Offlinedevice/Offlinedevice/3D/Pi5/Dock/readme

# Guide for Docking station for Offline device, Pi 5:

# Items needed for the build:
# * Small screwdriver and 6 pcs of M2 x 16 mm screws.
# * The 5 printed parts from the 3D files (optional also the dummy lid).
# * An official Raspberry PI 5 USB-power cable.
# * A HDMI- cable with micro-HDMI connector. Manufacturer: Zhonghua, Brand: TWOZOH, Model: ‎HD-012-1.0M
