Offlinedevice/Offlinedevice/3D/Pi5/Case/readme

# Case for:
# - Raspberry Pi 5
# - RTC battery
# - PN532 RFID module V3 
# - 5V 3007 Fan PWM Speed Adjustable CPU Cooling fan
# - Pi camera module 1, 2 or 3
