Offlinedevice/Offlinedevice/Bitcoin_wallet.png

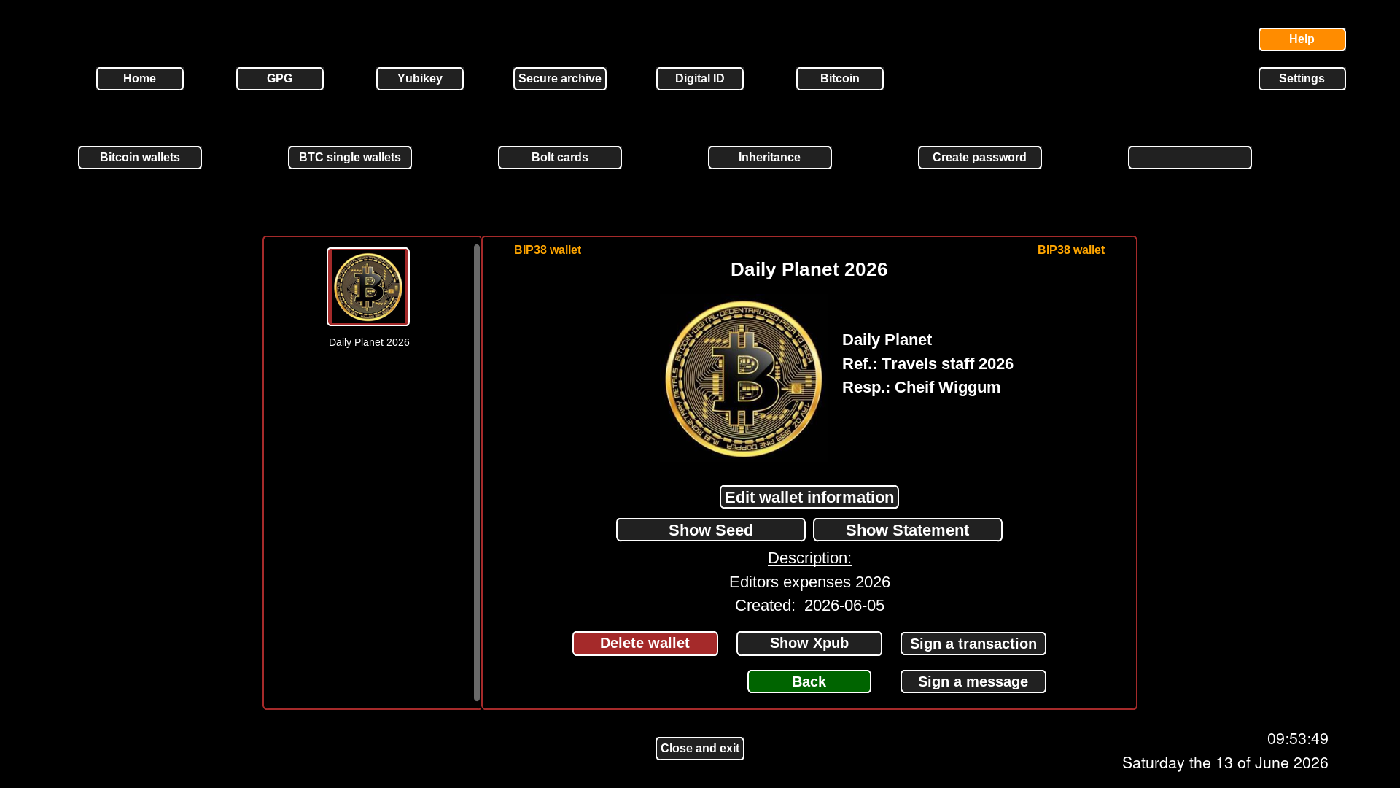
Bitcoin_wallet.png
