Offlinedevice/Offlinedevice/content/1_Welcome_Ethan_Soren.png

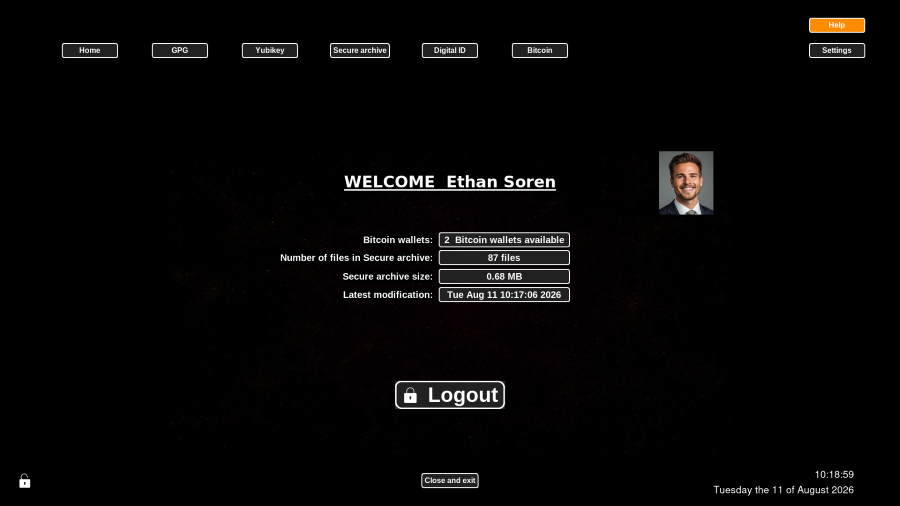
content/1_Welcome_Ethan_Soren.png
