Offlinedevice/Offlinedevice/content/3_1_Multisig_Signing_keys.PNG

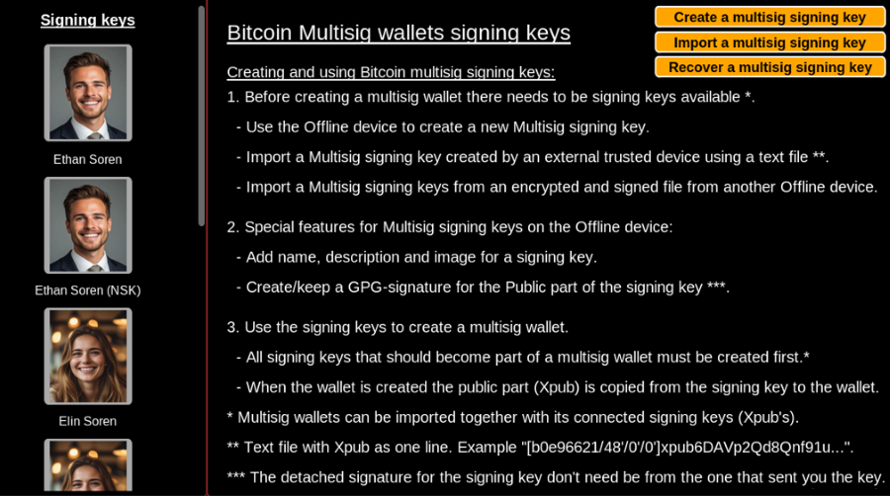
content/3_1_Multisig_Signing_keys.PNG
