Offlinedevice/Offlinedevice/images/black.jpg

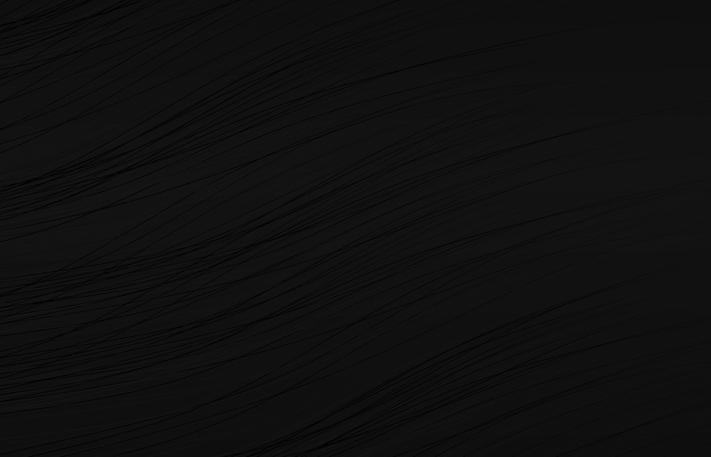
images/black.jpg
