Offlinedevice/Offlinedevice/images/blackbackground.jpg

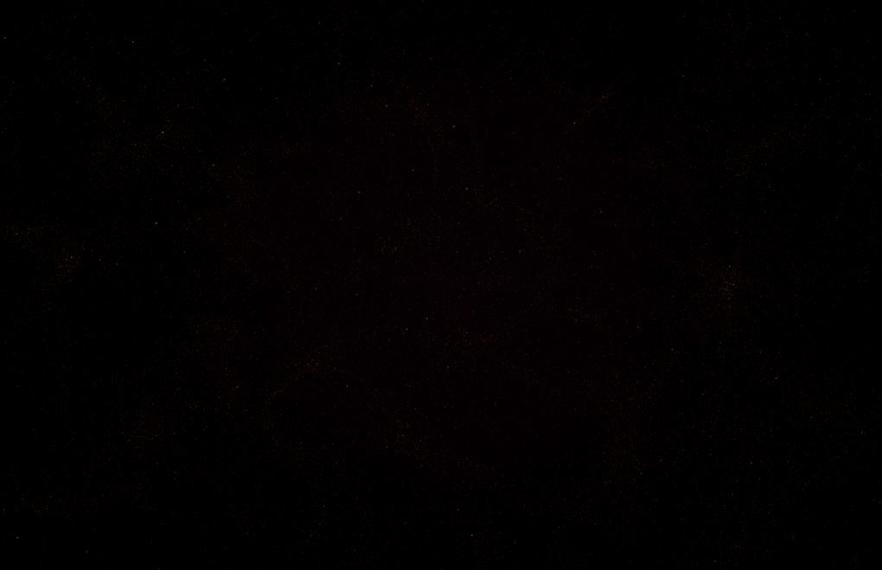
images/blackbackground.jpg
