Offlinedevice/Offlinedevice/images/bluebackground.jpg

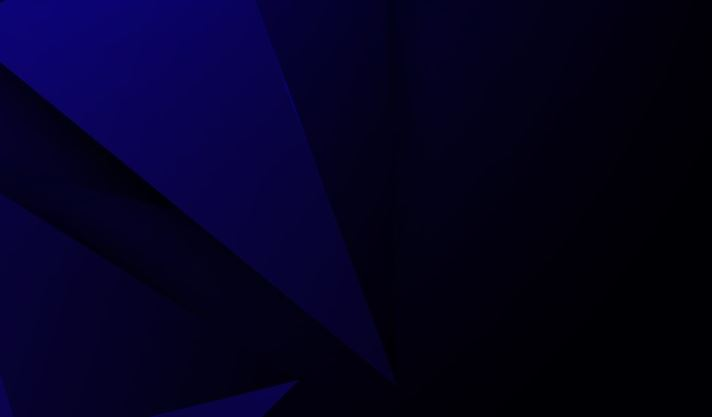
images/bluebackground.jpg
