Offlinedevice/Offlinedevice/images/bluewaves.jpg

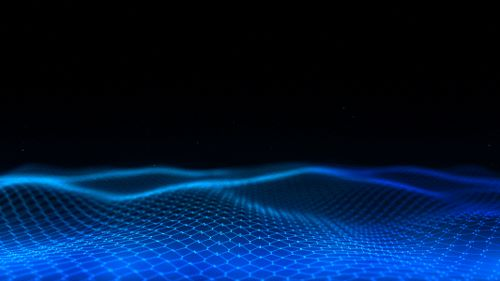
images/bluewaves.jpg
