Offlinedevice/Offlinedevice/images/boltcardbackground.JPG

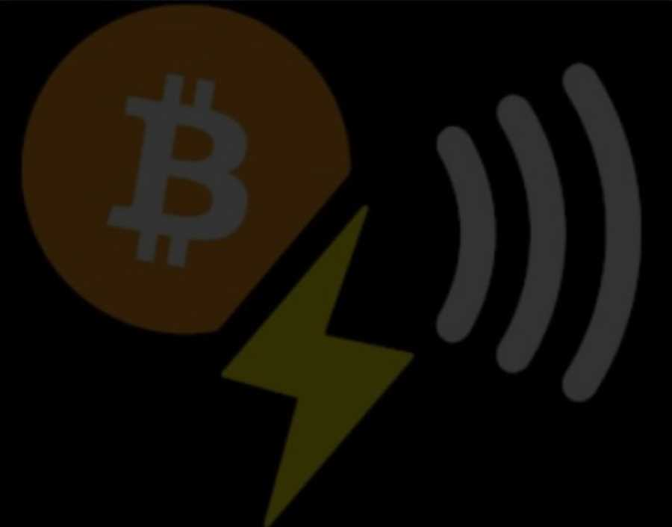
images/boltcardbackground.JPG
