Offlinedevice/Offlinedevice/images/darkbackground.jpg

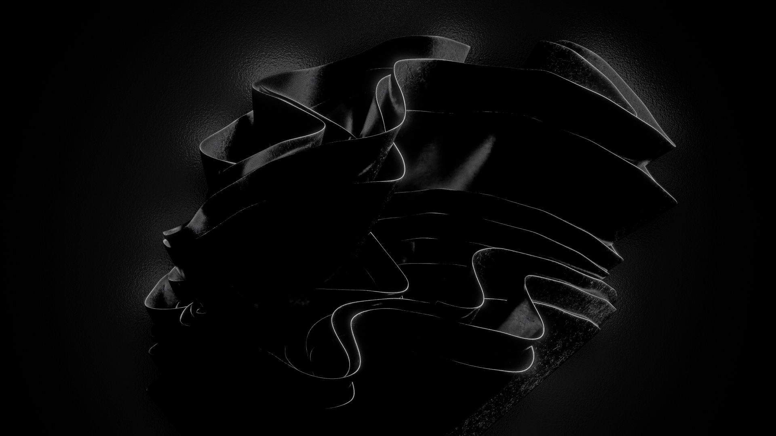
images/darkbackground.jpg
