Offlinedevice/Offlinedevice/images/darkbackgroundmid.jpg

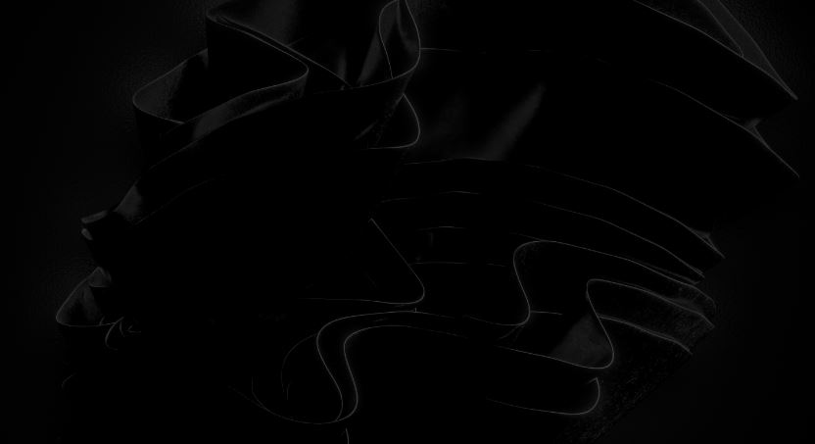
images/darkbackgroundmid.jpg
