Offlinedevice/Offlinedevice/images/GnuPGbackground.JPG

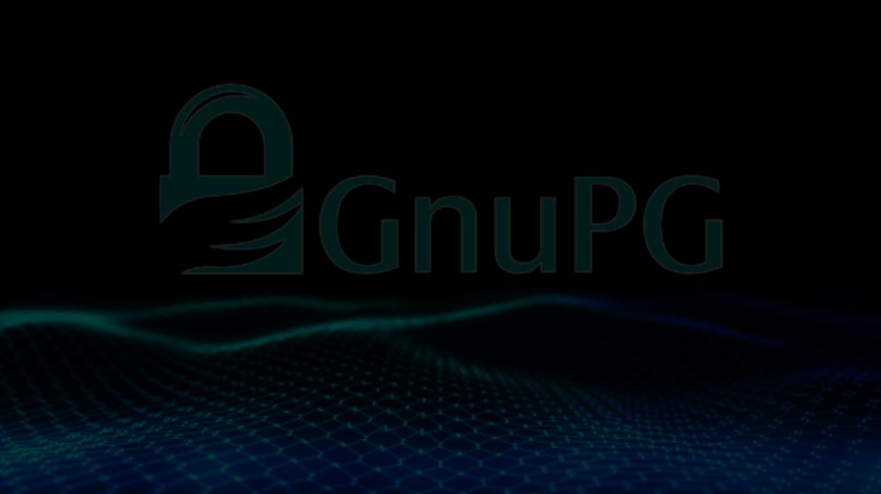
images/GnuPGbackground.JPG
