Offlinedevice/Offlinedevice/images/Inheritance_background.JPG

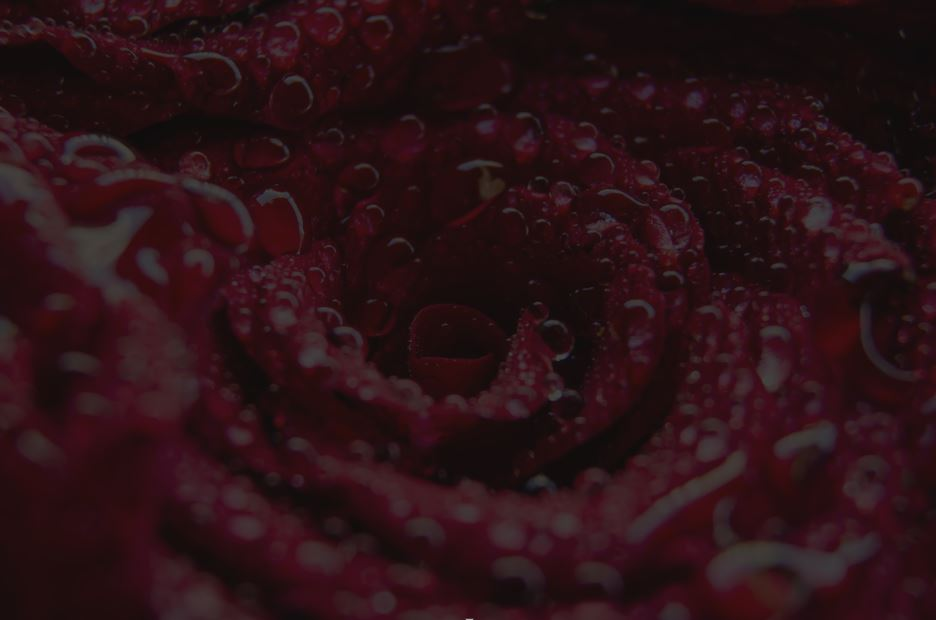
images/Inheritance_background.JPG
