Offlinedevice/Offlinedevice/images/lightbackgroundmid.jpg

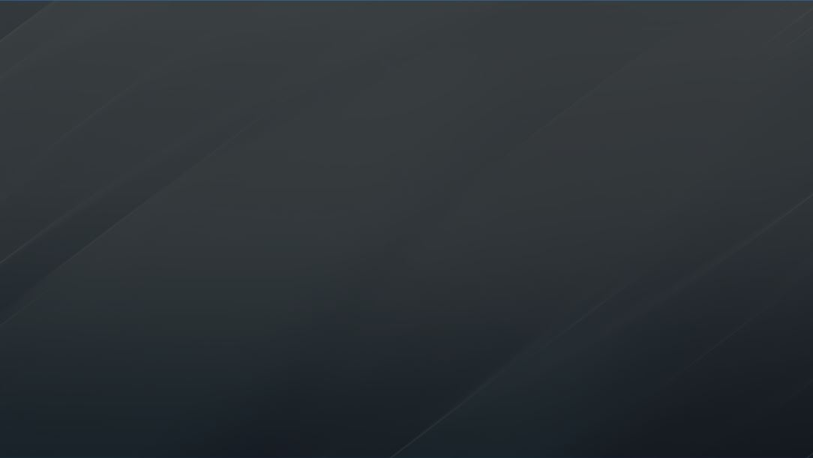
images/lightbackgroundmid.jpg
