Offlinedevice/Offlinedevice/images/summerbackground.jpg

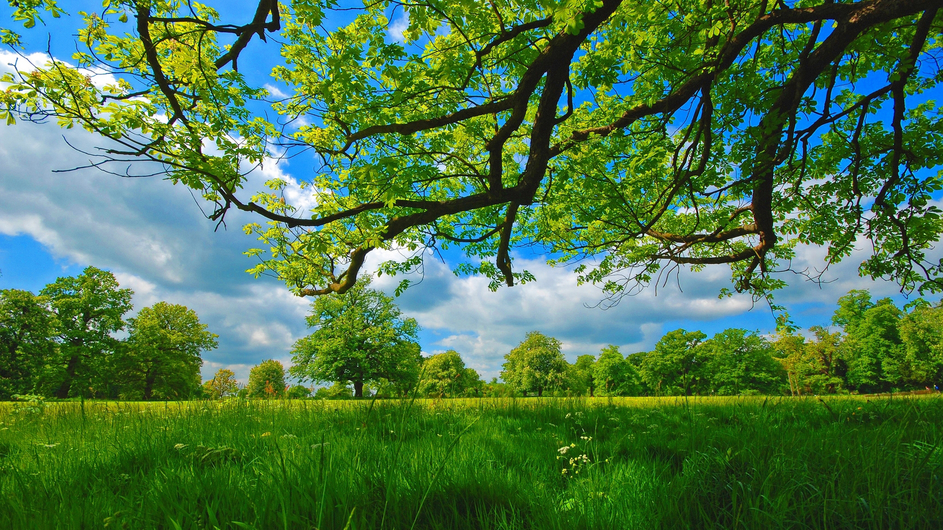
images/summerbackground.jpg
