Offlinedevice/Offlinedevice/images/summerbackgroundmid.jpg

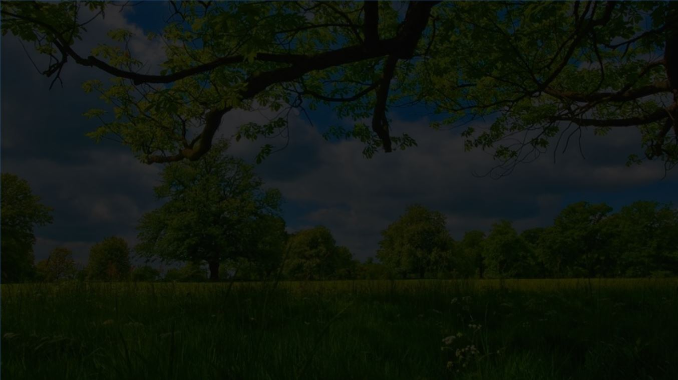
images/summerbackgroundmid.jpg
