Offlinedevice/Offlinedevice/images/vectorIDart.jpg

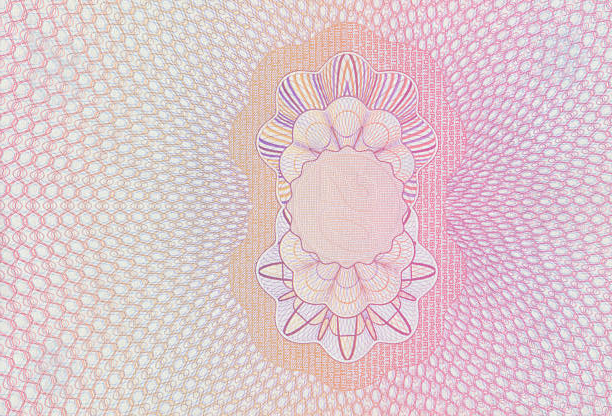
images/vectorIDart.jpg
