Offlinedevice/Offlinedevice/images/winterbackground.jpg

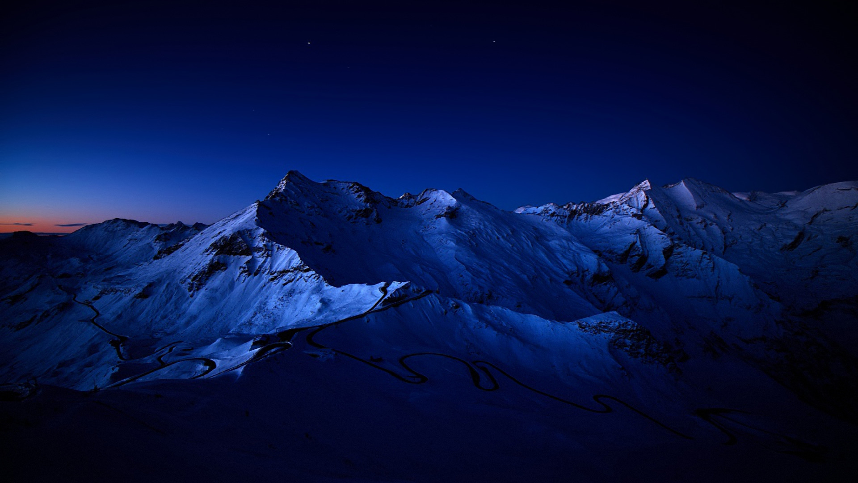
images/winterbackground.jpg
