Offlinedevice/Offlinedevice/images/winterbackgroundmid.jpg

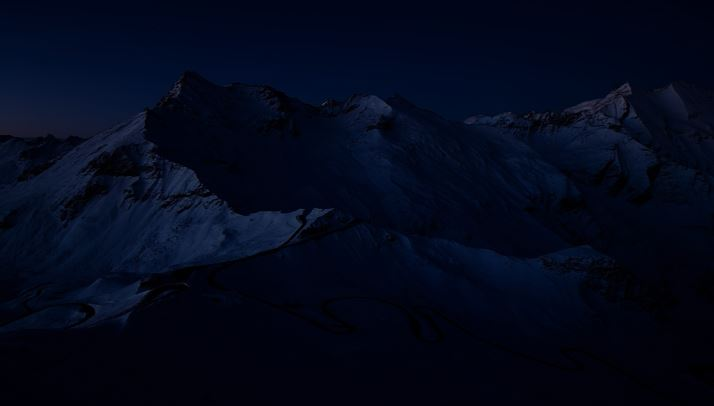
images/winterbackgroundmid.jpg
