Offlinedevice/Offlinedevice/images/Yubikey5CBackground.JPG

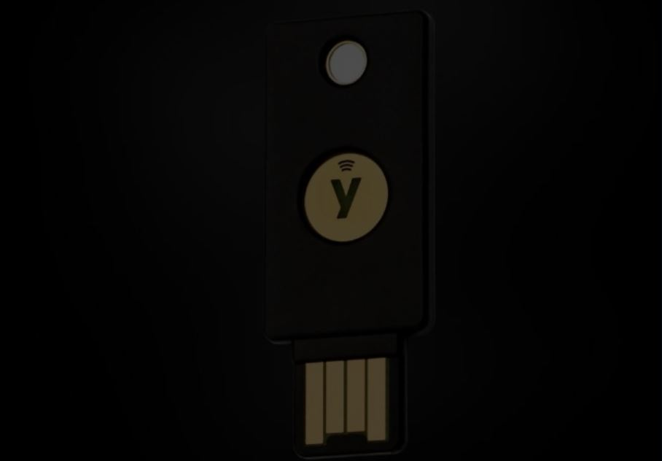
images/Yubikey5CBackground.JPG
