Offlinedevice/Offlinedevice/Pictures/AI_boy.png

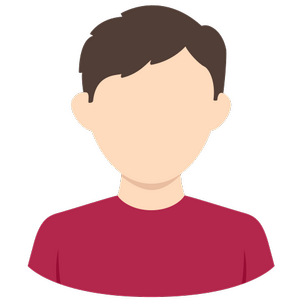
Pictures/AI_boy.png
