Offlinedevice/Offlinedevice/Pictures/AI_girl.png

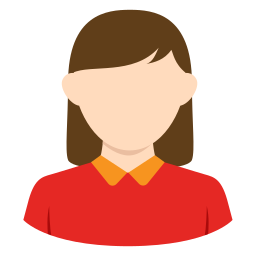
Pictures/AI_girl.png
