Offlinedevice/Offlinedevice/Pictures/AI_man.png

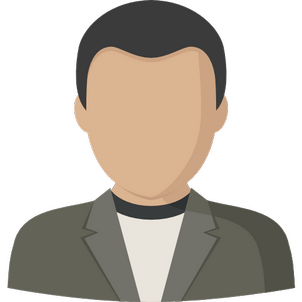
Pictures/AI_man.png
