Offlinedevice/Offlinedevice/Pictures/AI_woman.png

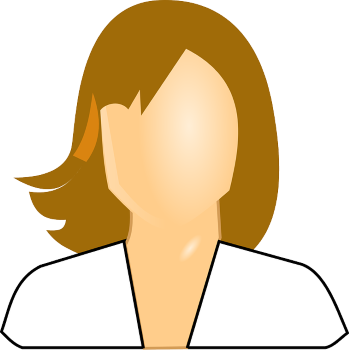
Pictures/AI_woman.png
