Offlinedevice/Offlinedevice/Pictures/user_anon.png

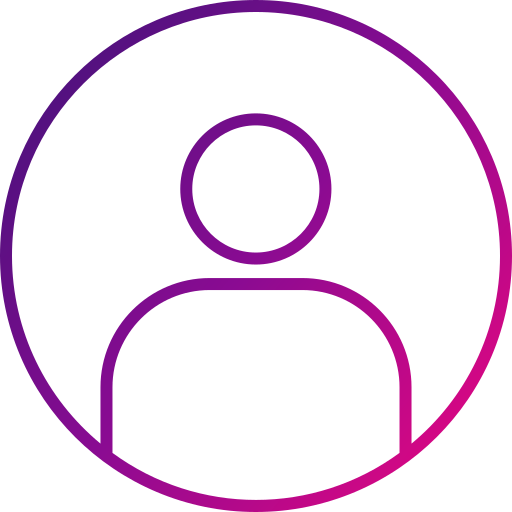
Pictures/user_anon.png
