Offlinedevice/Offlinedevice/Pictures/user_yinyang.png

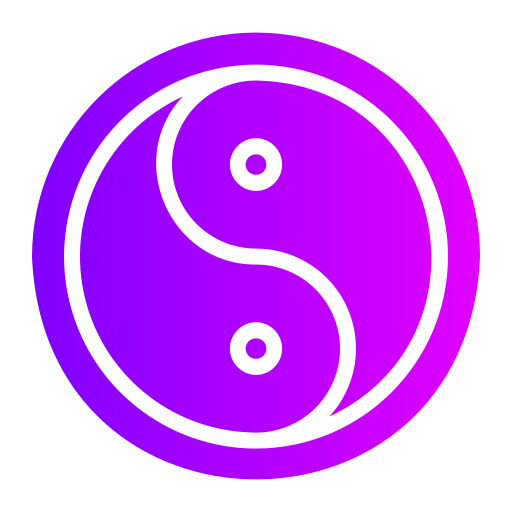
Pictures/user_yinyang.png
