Offlinedevice/Offlinedevice/3D/PiZero2W/Dock/Dock_lever_trim_mid-Body.stl

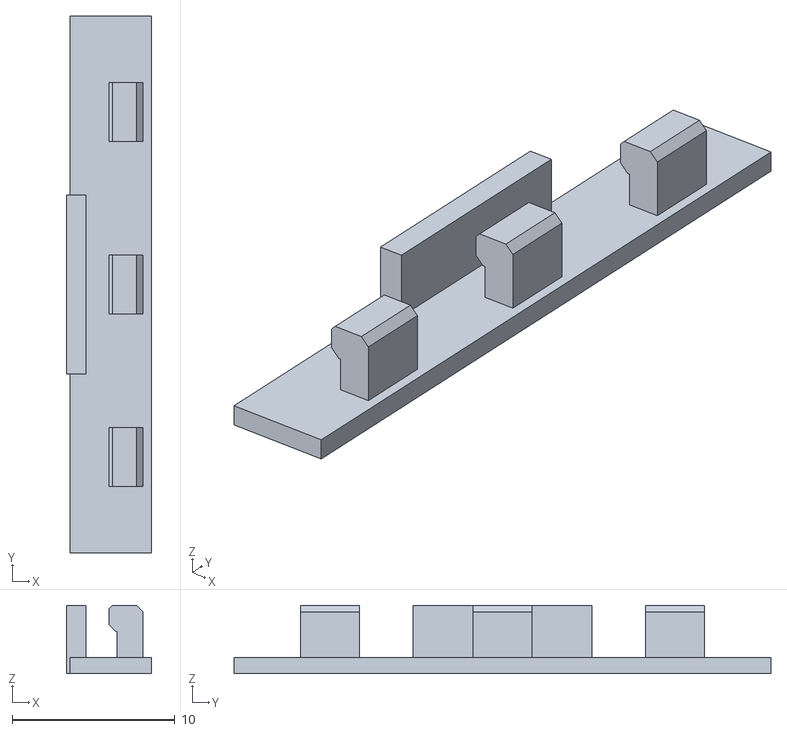
[picture p57: CAD file, 2026-07-20]
3D/PiZero2W/Dock/Dock_lever_trim_mid-Body.stl
5.20 x 33.0 x 4.20
