Offlinedevice/Offlinedevice/3D/SquareSafe/BackStop-Body.stl

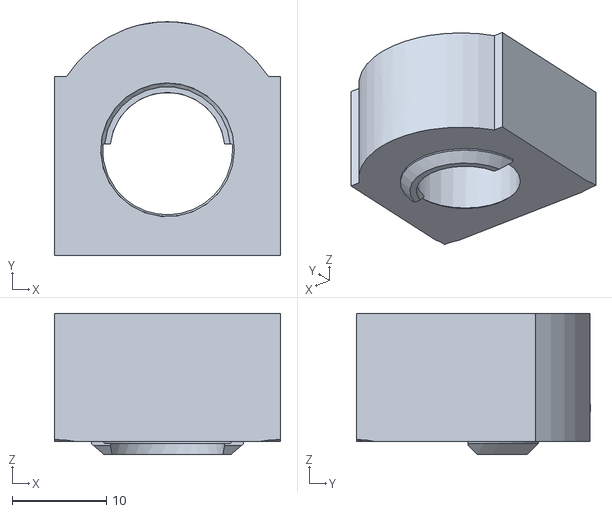
[picture p58: CAD file, 2026-09-15]
3D/SquareSafe/BackStop-Body.stl
24.0 x 24.8 x 15.0
