Offlinedevice/Offlinedevice/3D/HW_key/NFCKeyCap_LED_v2-Body.stl

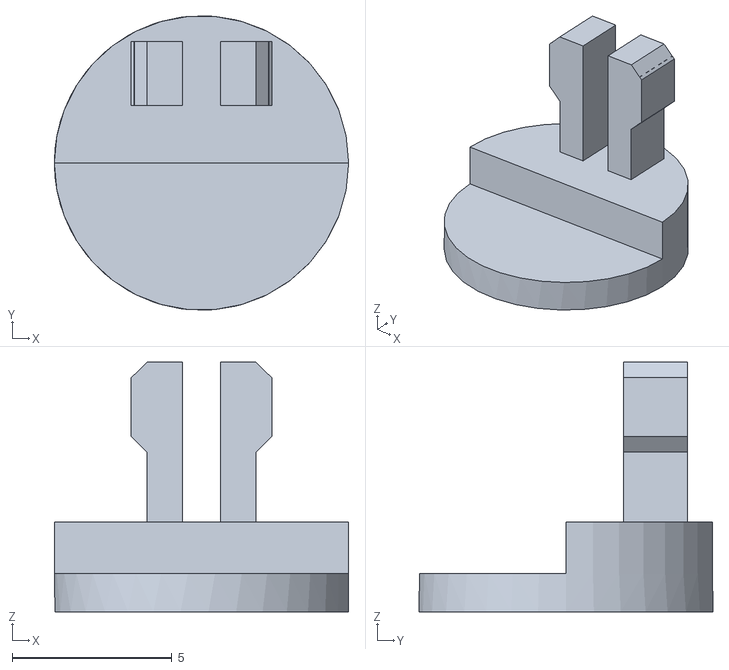
[picture p59: CAD file, 2026-06-12]
3D/HW_key/NFCKeyCap_LED_v2-Body.stl
9.20 x 9.19 x 7.80
