Offlinedevice/Offlinedevice/3D/Pi5/Dock/Dock_bottom_5_SSD_vent-Body.stl

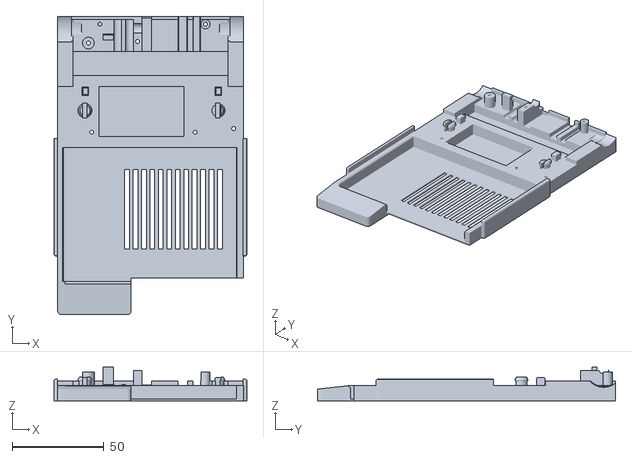
[picture p60: CAD file, 2026-08-19]
3D/Pi5/Dock/Dock_bottom_5_SSD_vent-Body.stl
105.0 x 162.2 x 18.4
