Offlinedevice/Offlinedevice/3D/PiZero2W/case/LidPIzeroBoxCamera_trim-Body.stl

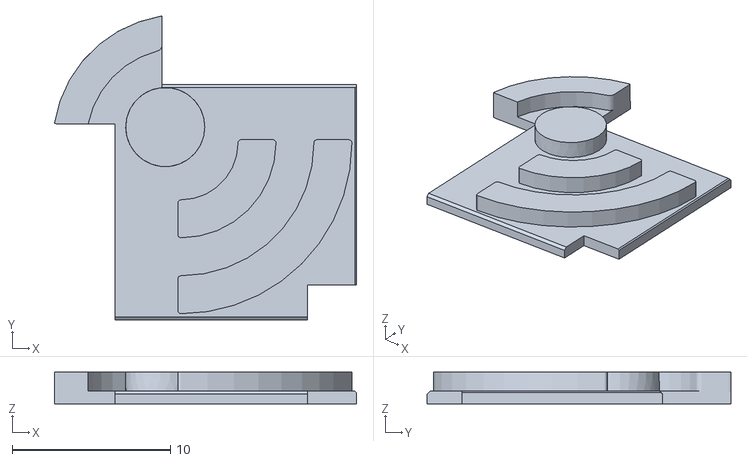
[picture p61: CAD file, 2026-07-27]
3D/PiZero2W/case/LidPIzeroBoxCamera_trim-Body.stl
19.1 x 19.2 x 2.00
