Offlinedevice/Offlinedevice/3D/PiZero2W/Dock/Dock_Pi2W_dummy_lid_with_trim-Body.stl

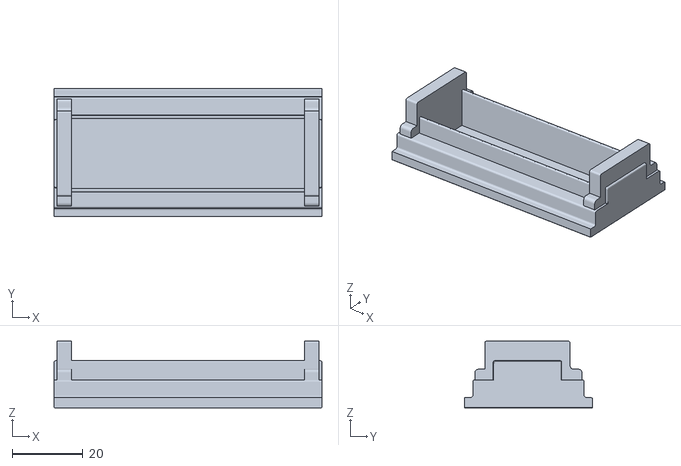
[picture p62: CAD file, 2026-07-20]
3D/PiZero2W/Dock/Dock_Pi2W_dummy_lid_with_trim-Body.stl
76.0 x 36.4 x 19.0
