Offlinedevice/Offlinedevice/3D/SquareSafe/InsertBox_90degree-Body.stl

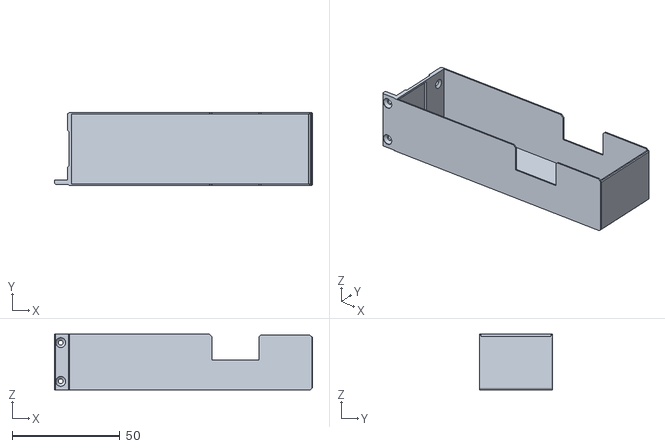
[picture p63: CAD file, 2026-09-15]
3D/SquareSafe/InsertBox_90degree-Body.stl
120.0 x 33.8 x 26.0
