Offlinedevice/Offlinedevice/3D/HW_key/NFCKeyBase_LED_v2-Body.stl

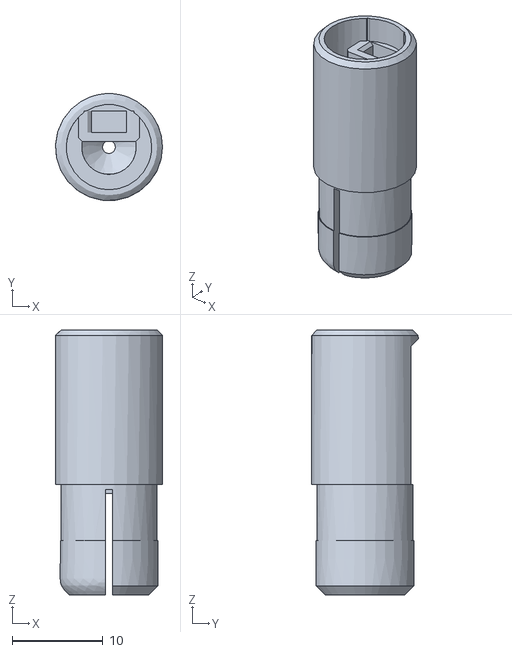
[picture p64: CAD file, 2026-06-12]
3D/HW_key/NFCKeyBase_LED_v2-Body.stl
11.8 x 11.8 x 29.2
