Offlinedevice/Offlinedevice/3D/Pi5/Case/Pi5_Bottom_LED_guide-Body.stl

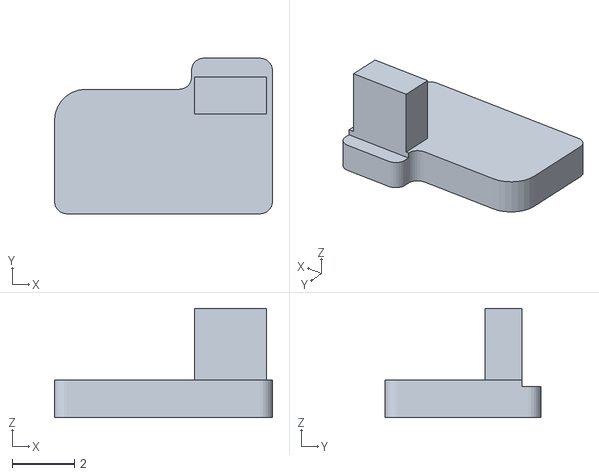
[picture p65: CAD file, 2026-05-22]
3D/Pi5/Case/Pi5_Bottom_LED_guide-Body.stl
7.00 x 5.00 x 3.50
