Offlinedevice/Offlinedevice/3D/Pi5/Dock/Dock_dummy_lid_5-Body.stl

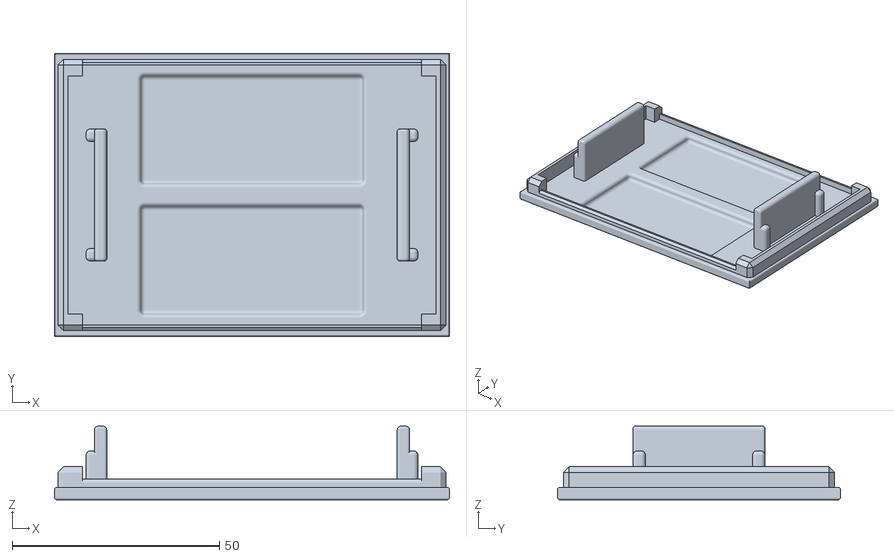
[picture p66: CAD file, 2026-06-12]
3D/Pi5/Dock/Dock_dummy_lid_5-Body.stl
95.2 x 68.2 x 17.8
