Offlinedevice/Offlinedevice/3D/PiZero2W/case/LidPIzeroBoxCamera3_RFID_high_with_trim-Body.stl

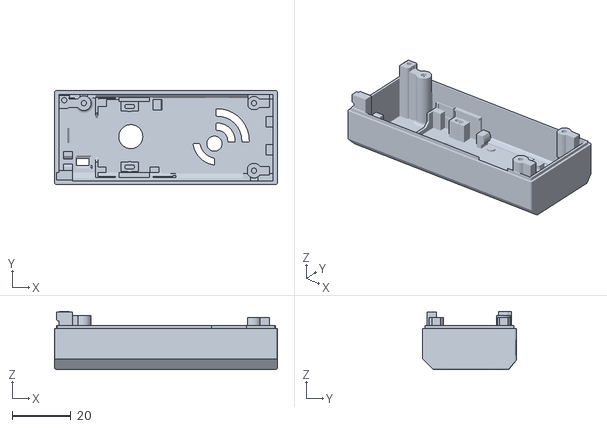
[picture p67: CAD file, 2026-07-27]
3D/PiZero2W/case/LidPIzeroBoxCamera3_RFID_high_with_trim-Body.stl
76.0 x 32.0 x 19.8
