Offlinedevice/Offlinedevice/3D/PiZero2W/Dock/Dock_lever_trim-Body.stl

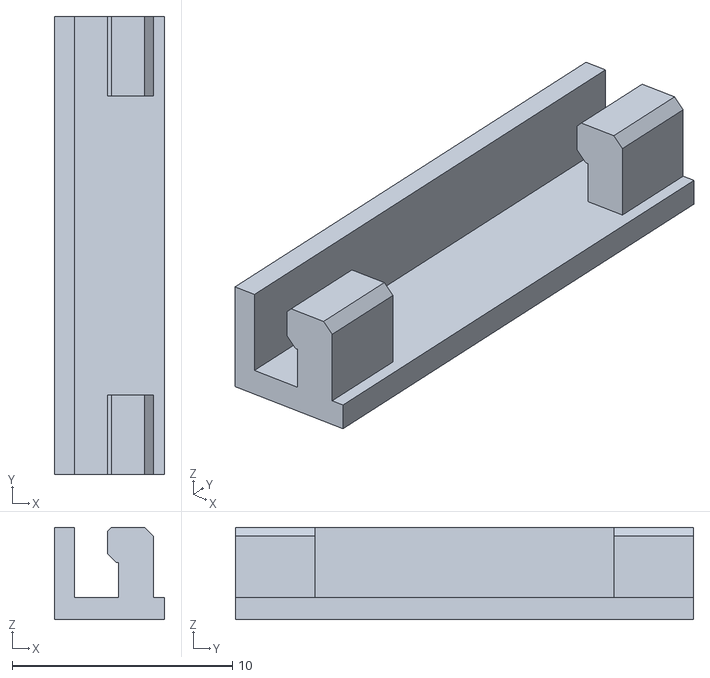
[picture p68: CAD file, 2026-07-20]
3D/PiZero2W/Dock/Dock_lever_trim-Body.stl
5.00 x 20.8 x 4.20
