Offlinedevice/Offlinedevice/3D/SquareSafe/InsertBox-Body.stl

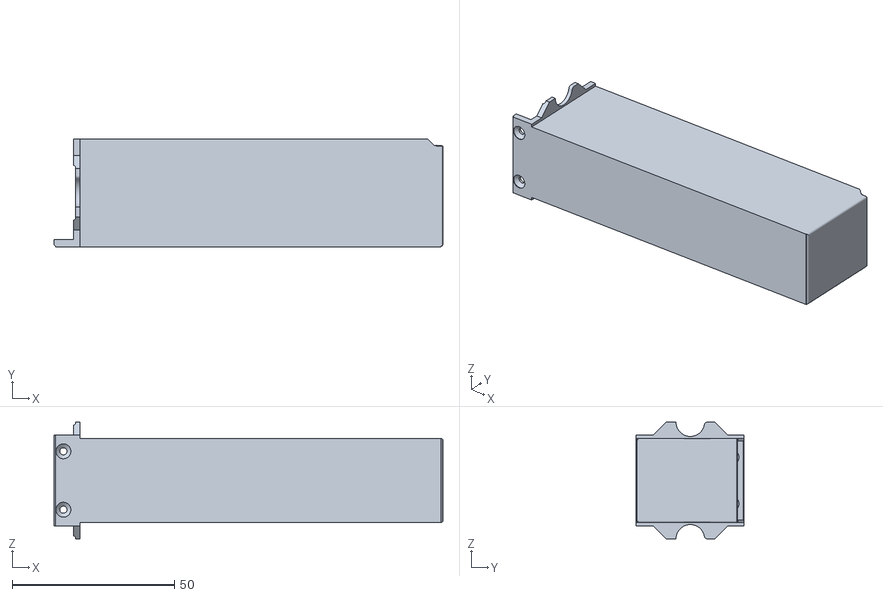
[picture p69: CAD file, 2026-09-04]
3D/SquareSafe/InsertBox-Body.stl
120.0 x 33.2 x 36.0
