Offlinedevice/Offlinedevice/3D/Pi5/Case/Fan_cover_v2-Body.stl

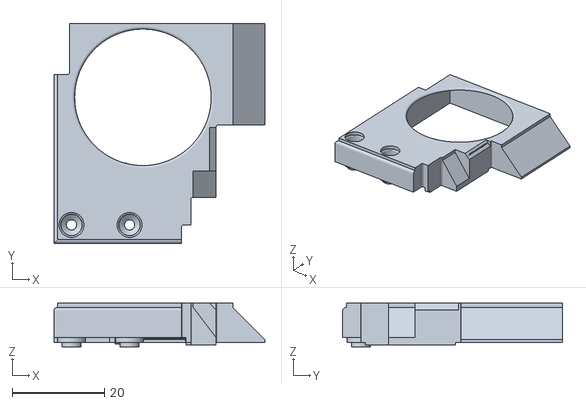
[picture p70: CAD file, 2026-05-22]
3D/Pi5/Case/Fan_cover_v2-Body.stl
45.8 x 47.7 x 9.50
