Offlinedevice/Offlinedevice/3D/Pi5/Dock/Cable_holder_5_15W-Body.stl

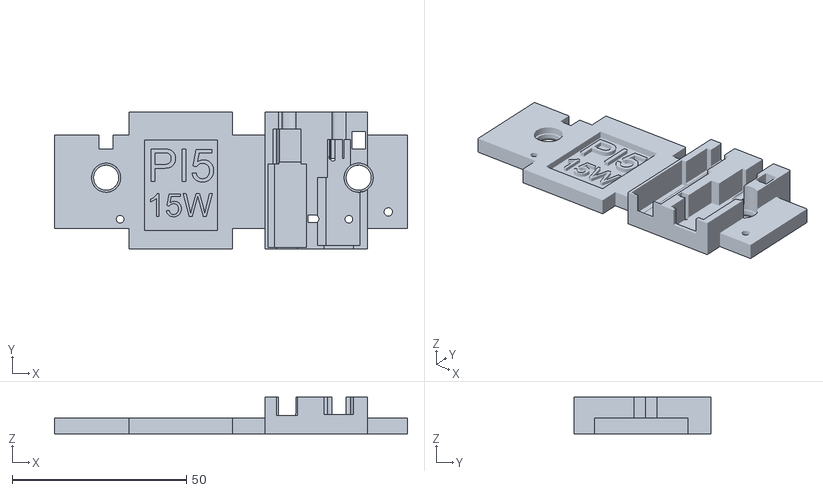
[picture p71: CAD file, 2026-06-05]
3D/Pi5/Dock/Cable_holder_5_15W-Body.stl
101.2 x 39.4 x 10.6
