Offlinedevice/Offlinedevice/3D/PiZero2W/Dock/Dock_sled-Body.stl

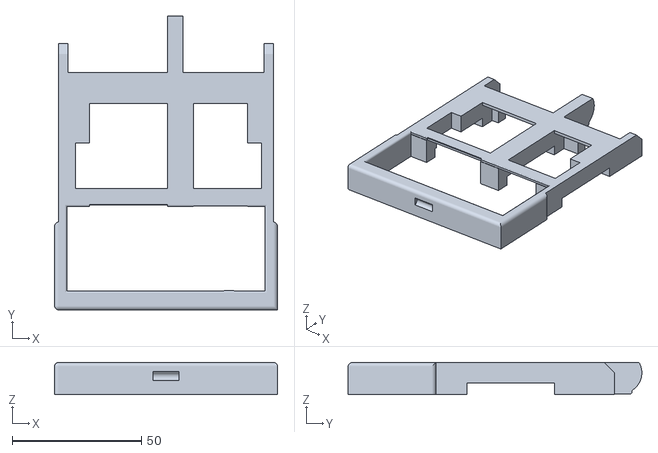
[picture p72: CAD file, 2026-07-20]
3D/PiZero2W/Dock/Dock_sled-Body.stl
86.4 x 113.8 x 12.4
