Offlinedevice/Offlinedevice/3D/SquareSafe/LockCase-Body.stl

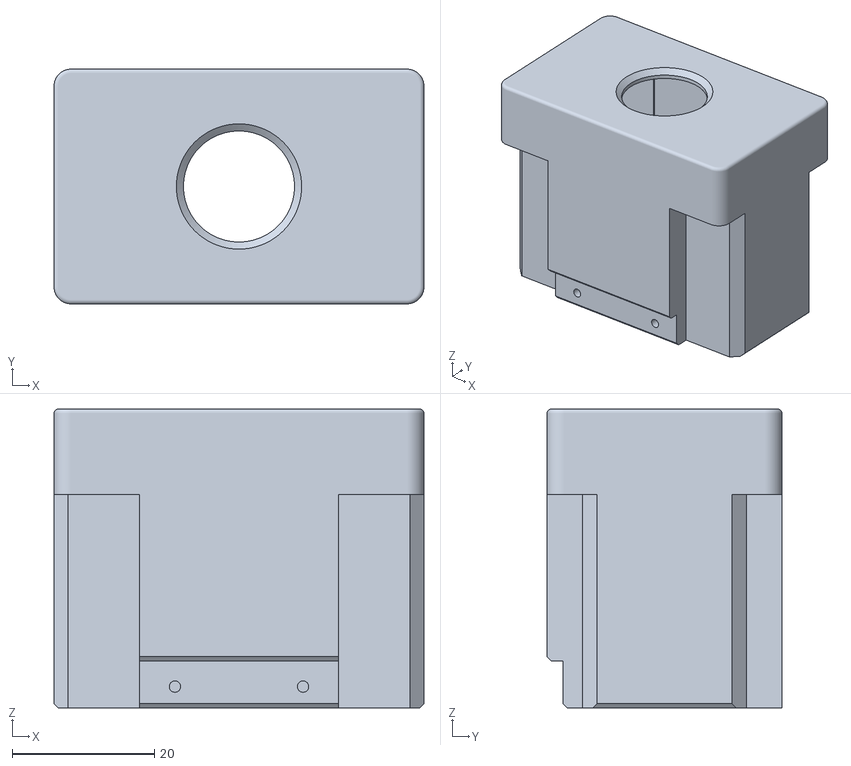
[picture p73: CAD file, 2026-09-04]
3D/SquareSafe/LockCase-Body.stl
52.0 x 33.0 x 42.0
