Offlinedevice/Offlinedevice/3D/Pi5/Case/Case_Pi5_fixing_bridge-Body002.stl

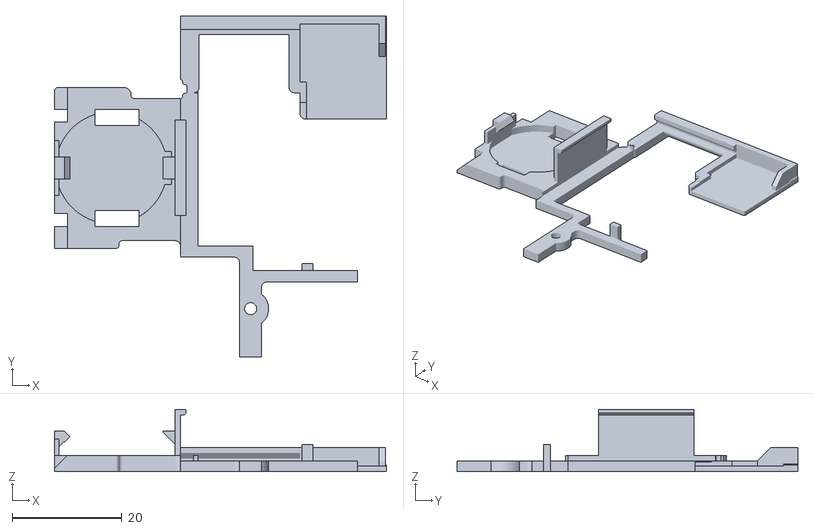
[picture p74: CAD file, 2026-05-22]
3D/Pi5/Case/Case_Pi5_fixing_bridge-Body002.stl
60.6 x 62.2 x 11.4
