Offlinedevice/Offlinedevice/3D/Pi5/Dock/Dock_lever_5_v2-Body.stl

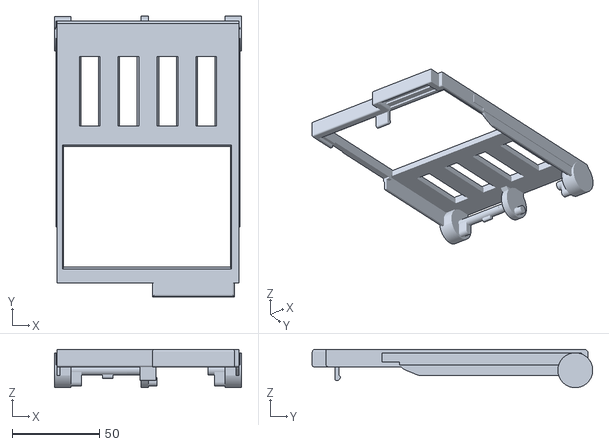
[picture p75: CAD file, 2026-06-05]
3D/Pi5/Dock/Dock_lever_5_v2-Body.stl
107.2 x 160.8 x 22.0
