Offlinedevice/Offlinedevice/3D/PiZero2W/case/PIzeroBoxRoundedCamera_trim-Body.stl

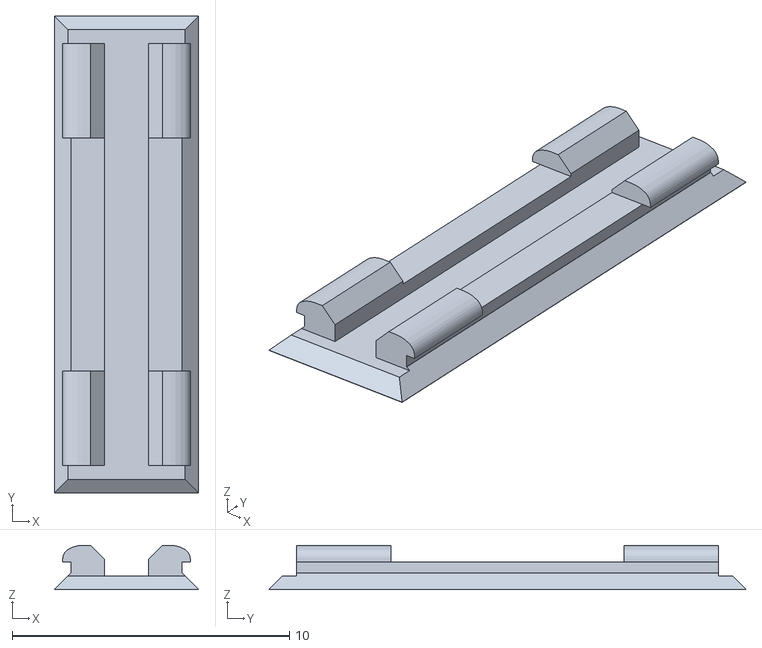
[picture p76: CAD file, 2026-07-20]
3D/PiZero2W/case/PIzeroBoxRoundedCamera_trim-Body.stl
5.20 x 17.2 x 1.60
