Offlinedevice/Offlinedevice/3D/PiZero2W/Dock/Cable_holder_trim-Body.stl

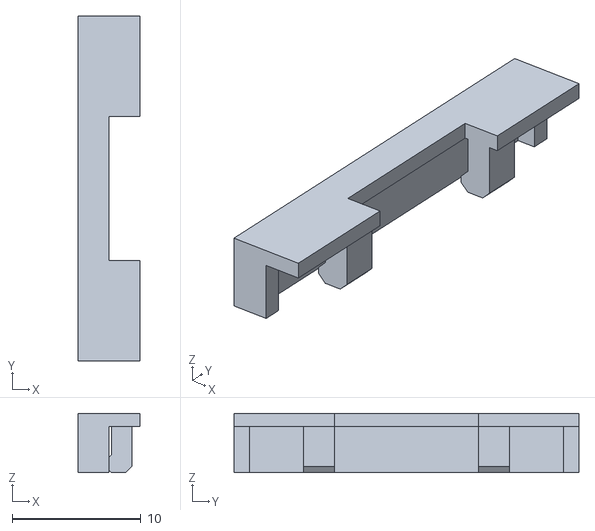
[picture p77: CAD file, 2026-07-20]
3D/PiZero2W/Dock/Cable_holder_trim-Body.stl
4.80 x 26.8 x 4.60
