Offlinedevice/Offlinedevice/3D/SquareSafe/Front-Body.stl

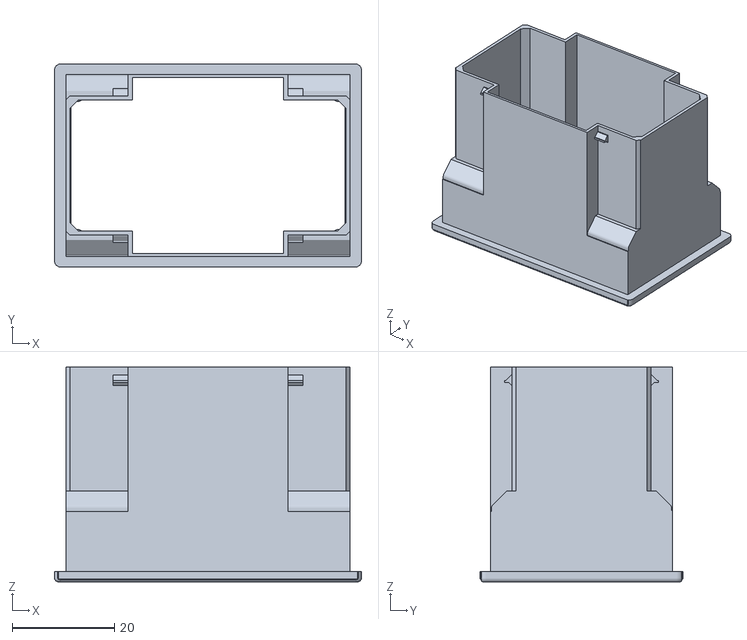
[picture p78: CAD file, 2026-09-04]
3D/SquareSafe/Front-Body.stl
60.0 x 39.6 x 42.0
