Offlinedevice/Offlinedevice/3D/Pi5/Dock/Dock_top_5-Body.stl

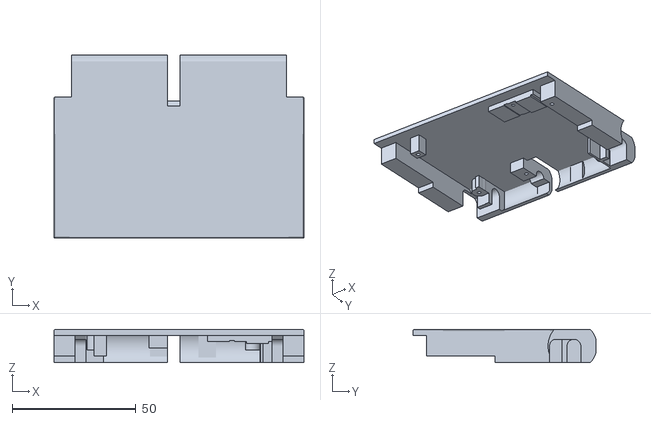
[picture p79: CAD file, 2026-05-22]
3D/Pi5/Dock/Dock_top_5-Body.stl
101.0 x 74.0 x 13.4
