Offlinedevice/Offlinedevice/3D/PiZero2W/Dock/Dock_lever_with_trim-Body.stl

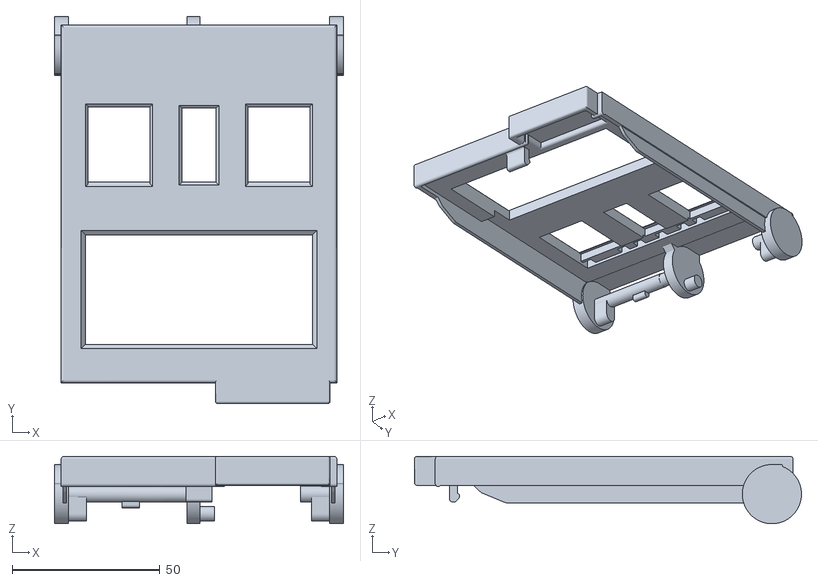
[picture p80: CAD file, 2026-07-20]
3D/PiZero2W/Dock/Dock_lever_with_trim-Body.stl
97.8 x 130.8 x 22.8
