Offlinedevice/Offlinedevice/3D/SquareSafe/Back-Body.stl

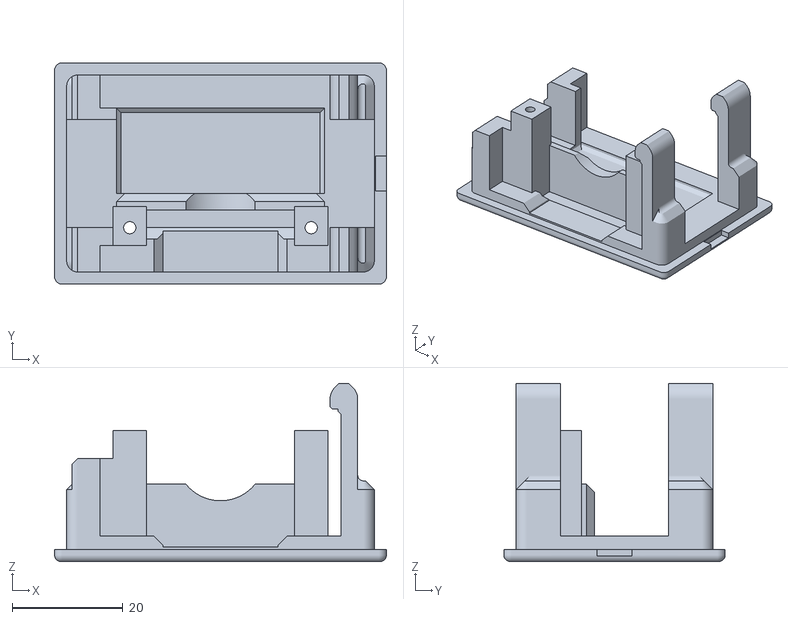
[picture p81: CAD file, 2026-09-04]
3D/SquareSafe/Back-Body.stl
60.0 x 40.0 x 32.2
