Offlinedevice/Offlinedevice/3D/PiZero2W/Dock/Dock_Pi2W_dummy_lid_trim-Body.stl

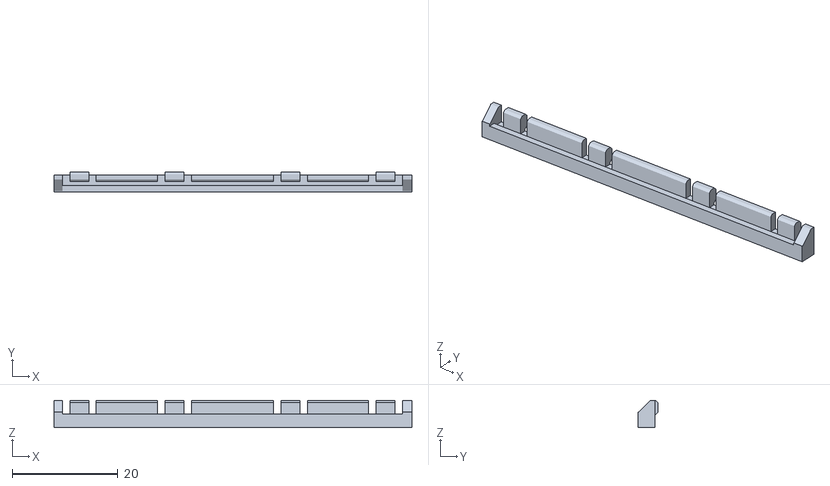
[picture p82: CAD file, 2026-07-20]
3D/PiZero2W/Dock/Dock_Pi2W_dummy_lid_trim-Body.stl
67.8 x 3.80 x 5.20
