Offlinedevice/Offlinedevice/3D/SquareSafe/AluTube_198mm_v2-Body.stl

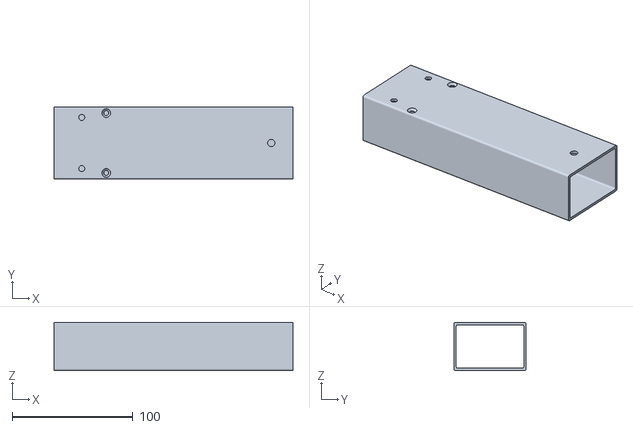
[picture p83: CAD file, 2026-08-30]
3D/SquareSafe/AluTube_198mm_v2-Body.stl
198.0 x 60.0 x 40.0
