Offlinedevice/Offlinedevice/3D/Pi5/Dock/Dock_sled_5-Body.stl

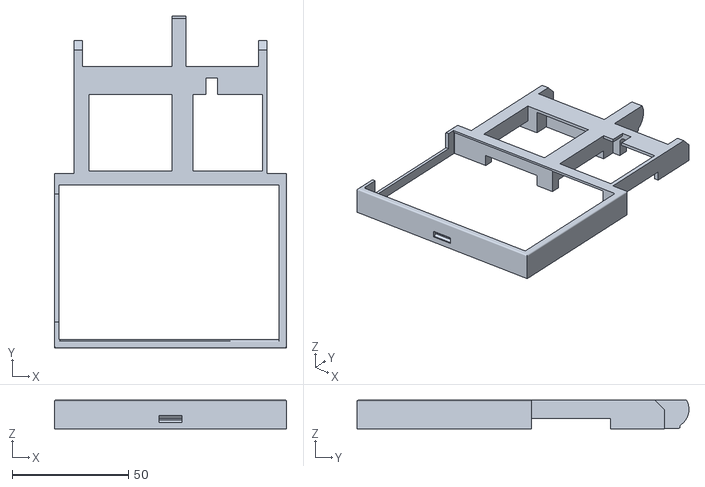
[picture p84: CAD file, 2026-02-28]
3D/Pi5/Dock/Dock_sled_5-Body.stl
100.0 x 143.0 x 12.4
