Offlinedevice/Offlinedevice/3D/PiZero2W/case/LEDguide_high-Body.stl

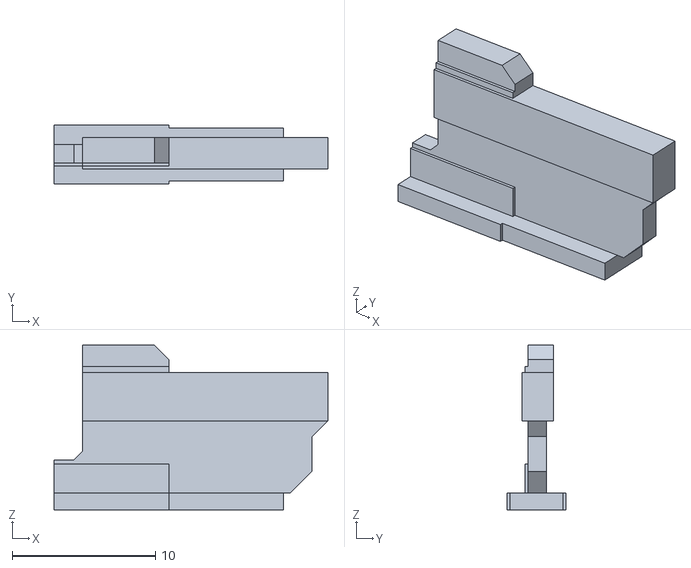
[picture p85: CAD file, 2026-05-22]
3D/PiZero2W/case/LEDguide_high-Body.stl
19.1 x 4.10 x 11.5
