Offlinedevice/Offlinedevice/3D/PiZero2W/Dock/Dock_Pi2W_dummy_lid-Body.stl

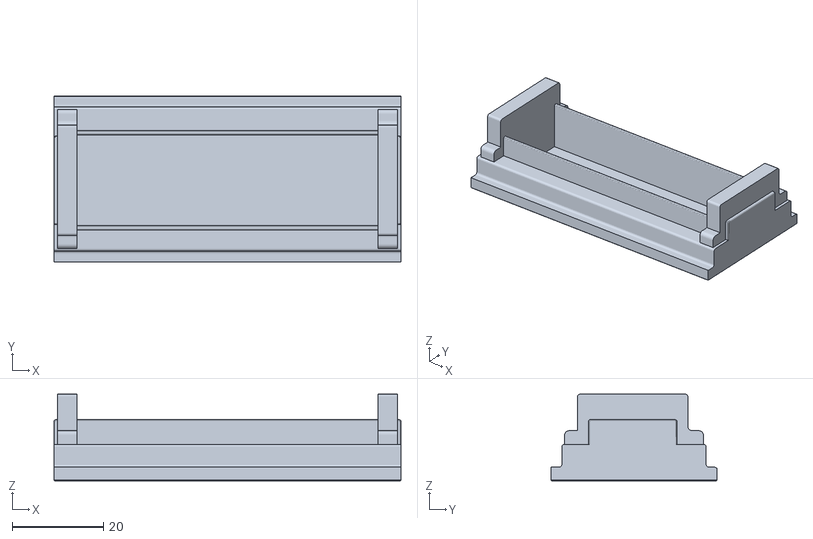
[picture p86: CAD file, 2026-07-20]
3D/PiZero2W/Dock/Dock_Pi2W_dummy_lid-Body.stl
76.0 x 36.4 x 19.0
