Offlinedevice/Offlinedevice/3D/SquareSafe/LockCase_Lid-Body.stl

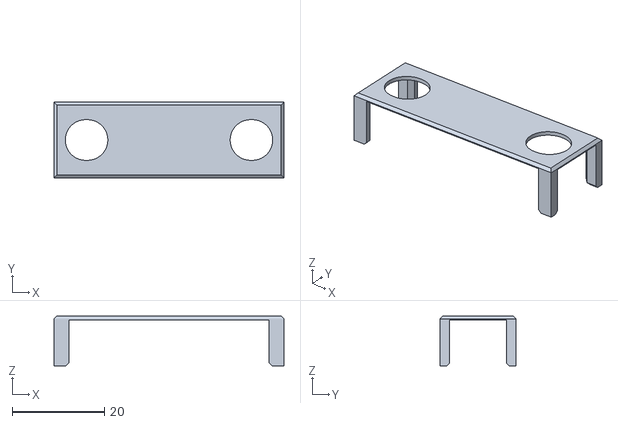
[picture p87: CAD file, 2026-08-30]
3D/SquareSafe/LockCase_Lid-Body.stl
49.8 x 16.4 x 10.8
