Offlinedevice/Offlinedevice/3D/PiZero2W/Dock/Dock_bottom-Body.stl

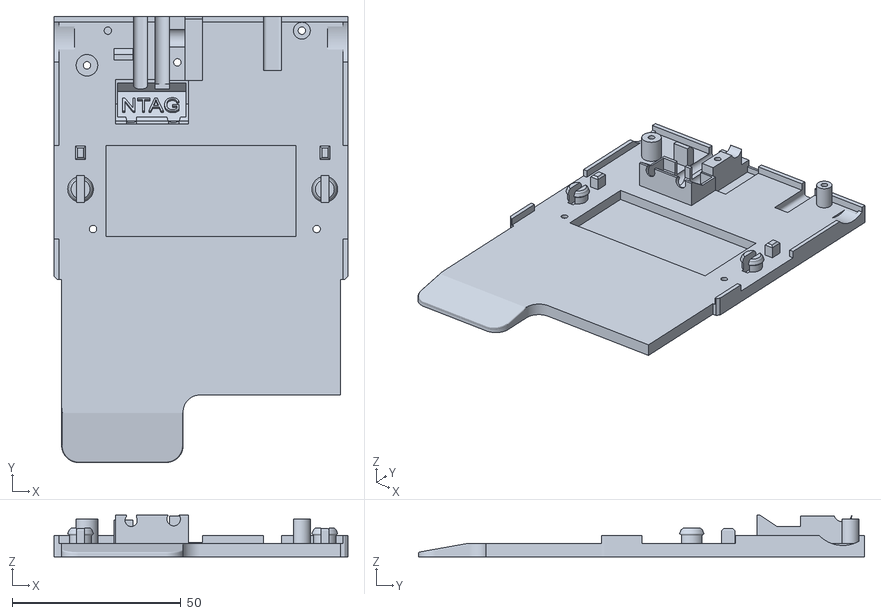
[picture p88: CAD file, 2026-07-20]
3D/PiZero2W/Dock/Dock_bottom-Body.stl
87.0 x 132.2 x 12.4
