Offlinedevice/Offlinedevice/3D/PiZero2W/Dock/Dock_top-Body.stl

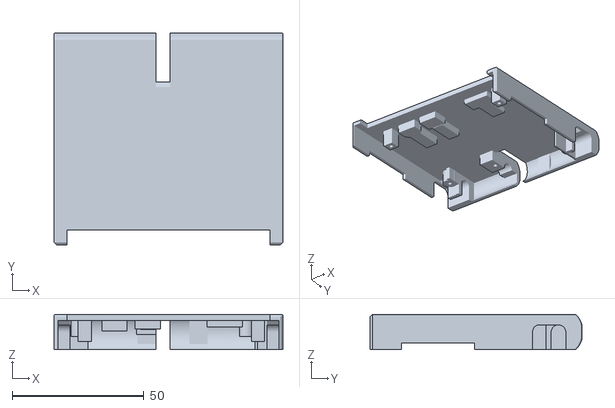
[picture p89: CAD file, 2026-05-22]
3D/PiZero2W/Dock/Dock_top-Body.stl
87.0 x 80.6 x 13.4
