Offlinedevice/Offlinedevice/3D/PiZero2W/Dock/Cable_holder-Body.stl

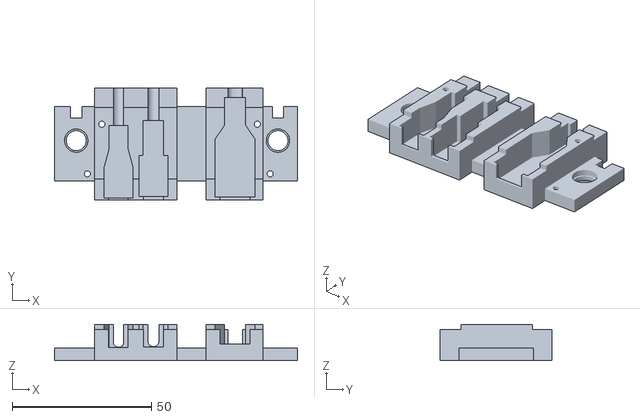
[picture p90: CAD file, 2026-02-28]
3D/PiZero2W/Dock/Cable_holder-Body.stl
87.2 x 40.2 x 13.0
