Offlinedevice/Offlinedevice/code/GUIApp.py

#!/usr/bin/env python3
#
#  GUIApp.py
#  Version:0.2.6
#  Git repo: https://github.com/Offlinedevice
#  Offline Device for:
#     Managing GPG local keychain
#     Managing Yubikey 5C NFC. OpenPGP and FIDO2 etc
#     Managing secure and redundant backup for files, accounts and crypto wallets etc
#     Generating offline wallets (and store backup's)
#     Generating and managing private digital ID's (under construction)
#     Managing Bolt Cards for BTC payments 
#     Managing FIDO2 keys for passwordless login
#  
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
#  You should have received a copy of the GNU General Public License along with this program. If not, see <https://www.gnu.org/licenses/>.

#  SPDX-License-Identifier: GPL-2.0-only
#  GUIApp.py - Offline device.
#  Copyright (c) 2024 

import sys
import tkinter as tk
from tkinter import *
from tkinter import messagebox, ttk
from tkinter import filedialog
from tkinter import simpledialog
from pathlib import Path
import customtkinter as ctk
from PIL import Image, ImageTk
import gnupg
import shutil
import gzip
import webbrowser
import os
import os.path, time
import glob
import tarfile
import yubico
import usb.core
import usb.backend.libusb1
import subprocess
import time
from datetime import date
from tkcalendar import Calendar,DateEntry 
from tktimepicker import AnalogPicker, AnalogThemes,constants
import csv
import bip32utils
from mnemonic import Mnemonic
import bech32
import base58
from datetime import datetime
from typing import Optional
import hashlib
from functools import partial
import qrcode
import boltlib
from random import SystemRandom
from pywallet import wallet
import pyscreenshot as ImageGrab

check_var = ' '
my_text_buffer = ' '
path_to_USB_secure = 'Secure USB folder is not available'
PersonalGPGKey = ''
CommunicationGPGKey = ''
clicked_privateKey = ' '
clicked_privateSubKey = ' '
clicked_communicationKey = ' ' 
filepathdestinationfolder = '/home/user1'
commkey = ' '
timeSecUSBLastModified = '<Unknown>'
softwareVersion = '0.2.6'
softwareStatus = 'Beta'
HelpBodyVisible = False
newIDflag = False
statt = True 
ctk.set_appearance_mode("dark")
ctk.set_default_color_theme("dark-blue")

text_file_data = ' '
s_width = 0
s_height = 0
U2F_VENDOR_FIRST = 0x40

System_button_color = 'DarkBlue'
GPG_button_color = 'green'
SecUSB_button_color = 'purple'
Yubikey_button_color = 'red'
DigitalID_button_color = 'brown'
Boltcard_button_color = 'brown'
Help_button_color = 'orange'
			
# FIPS specific INS values
INS_FIPS_VERIFY_PIN = U2F_VENDOR_FIRST + 3
INS_FIPS_SET_PIN = U2F_VENDOR_FIRST + 4
INS_FIPS_RESET = U2F_VENDOR_FIRST + 5
INS_FIPS_VERIFY_FIPS_MODE = U2F_VENDOR_FIRST + 6
  
class App(ctk.CTk):
	def __init__(self):
		global s_width, s_height
		#main setup
		super().__init__()
		self.title("Offline Device GUI")
		s_width = self.winfo_screenwidth()
		s_height = self.winfo_screenheight()
		geom = str(s_width) + 'x' + str(s_height)
		self.geometry(geom)
		self.wm_attributes('-fullscreen', True)
		#self.wm_attributes('-type', 'splash')
		
		self.state('normal')
		self.option_add('*Dialog.msg.font', 'Helvetica 14')
		# widget
		self.menu = Menu(self)
		
		self.mainloop()
		
class Menu(ctk.CTkFrame):	
	def msg_box_textbox(self, msg_text, size_width, size_height):
		global meny
		pop = Toplevel()
		pop.title("Information")
		box_size = size_width + 'x' + size_height
		pop.geometry(box_size)
		pop.focus()
		pop.grab_set()
		
		pop.config(bg="grey")
		
		my_text = ctk.CTkTextbox(pop, width=int(size_width), height=int(size_height), corner_radius=1, border_width=2, border_color="black", border_spacing=10, fg_color="light grey", text_color="black", font=("Arial", 16), wrap="word", activate_scrollbars = True, scrollbar_button_color="blue", scrollbar_button_hover_color="red")
		my_text.insert('end', msg_text)
	
		my_text.configure(state="disabled")
		my_text.place(relx=0.5, rely=0.5, anchor="center")		
			
		def exit_msg():
			pop.destroy()
			
		def stay_on_top():
			pop.lift()
			pop.after(1000, stay_on_top)	
		ok_button = ctk.CTkButton(pop, text="OK", text_color="black", fg_color="light grey", border_width=2, border_color="black", command=exit_msg)
		ok_button.place(relx=0.5, rely=0.9, anchor="center")
		stay_on_top()
		
	def __init__(self, parent):
		super().__init__(parent)
		global s_width,s_height
		self.place(x=0, y=0, relwidth = 1, relheight = 1)
		
		my_image = ctk.CTkImage(light_image=Image.open('/home/user1/venvpython/images/blue.jpg'), dark_image=Image.open('/home/user1/venvpython/images/blue.jpg'), size=(s_width,s_height))
		
		my_label = ctk.CTkLabel(self, text="", image=my_image)
		my_label.pack()

		self.create_meny()
				
	def encryptanddestroy(self):
	
		global path_to_USB_secure
		global timeSecUSBLastModified
		global filepathdestinationfolder
		global PersonalGPGKey
		global s_width,s_height
		
		#The big frame
		my_big_Frame = ctk.CTkFrame(self, 
		width=s_width, 
		height=s_height,
		border_width=1,
		border_color="blue"
		)
		my_big_Frame.place(relx=0.5, rely=0.5, anchor="center")
		
		pathtobackg = "/home/user1/venvpython/images/blue.jpg"
		backg = ctk.CTkImage(light_image=Image.open(pathtobackg), dark_image=Image.open(pathtobackg), size=(s_width, s_height))
		Label_backg = ctk.CTkLabel(my_big_Frame, image=backg, text = "")
		Label_backg.place(x=0, y=0)
		Label_backg.focus_set()
		Label_backg.focus_force()
		
		my_big_Frame.focus_set()
		my_big_Frame.focus_force()
		
		my_font = ctk.CTkFont(family="Arial", size=28, weight="bold", slant="roman", underline=False, overstrike=False)
		
		infoLabel = ctk.CTkLabel(my_big_Frame, text="Encrypting the device and shutting down...", text_color="white", font=my_font, fg_color="navy blue")
		infoLabel.place(relx=0.5, rely=0.42, anchor="center")
			
		gpg = gnupg.GPG(gnupghome='/home/user1/.gnupg/')
		
		print(PersonalGPGKey)
		
		if path_to_USB_secure == 'Secure USB folder is available':
			
			full_path = str(filepathdestinationfolder) + "/secure/"
			compressed_file = shutil.make_archive(full_path, 'gztar', full_path)
			# Encrypt the tarfile and remove the unencrypted tarfile
			encrypted_data = gpg.encrypt_file(compressed_file, PersonalGPGKey, always_trust=True) 
			
			cmd = 'shred -zu -n7 ' + filepathdestinationfolder + "/" + "secure.tar.gz"
			os.system(cmd)

			# Write the encrypted file to disk
			compressedoutfile = open(filepathdestinationfolder + "/" + PersonalGPGKey + 'securefolder.tar.gz.gpg', 'w')
			compressedoutfile.write(str(encrypted_data))
			compressedoutfile.close()
			full_path = str(filepathdestinationfolder) + "/secure"
			cmd = 'find ' +  full_path + ' -type f -exec shred -zu {} \\;'
			os.system(cmd)
			cmd = 'rm -r ' +  full_path
			os.system(cmd)
			os.system('sudo shutdown -h now')
			#sys.exit(0)
		else:
			os.system('sudo shutdown -h now')
			#sys.exit(0)
			
	def set_colors(self, color):
		global System_button_color
		global GPG_button_color
		global SecUSB_button_color
		global Yubikey_button_color
		global DigitalID_button_color
		global Boltcard_button_color
		global Help_button_color
		
		if color != 'Varied':
			System_button_color = color
			GPG_button_color = color
			SecUSB_button_color  = color
			Yubikey_button_color  = color
			DigitalID_button_color = color
			Boltcard_button_color = color
			Help_button_color = color
		else:
			System_button_color = 'DarkBlue'
			GPG_button_color = 'green'
			SecUSB_button_color = 'purple'
			Yubikey_button_color = 'red'
			DigitalID_button_color = 'brown'
			Boltcard_button_color = 'brown'
			Help_button_color = 'orange'
			
		#self.create_meny()
				
	def create_meny(self):
		global s_width,s_height
		global System_button_color
		global GPG_button_color
		global SecUSB_button_color
		global Yubikey_button_color
		global DigitalID_button_color
		global Boltcard_button_color
		global Help_button_color
		
		#The big frame
		my_big_Frame = ctk.CTkFrame(self, 
		width=s_width, 
		height=s_height,
		border_width=1,
		border_color="blue"
		)
		my_big_Frame.place(relx=0.5, rely=0.5, anchor="center")
		
		pathtobackg = "/home/user1/venvpython/images/blue.jpg"
		
		if path_to_USB_secure == 'Secure USB folder is available':			
			completeName = str(filepathdestinationfolder) + "/secure/settings.csv"
			try:
				with open(completeName, 'r') as file:
					csvfile = csv.reader(file)
					for lines in csvfile:
						if lines:	
							users_theme = lines[1]
							users_colors = lines[2]
			except FileNotFoundError:
				messagebox.showinfo("Information", "No settings file found.")
			if users_theme == 'Winter':
				pathtobackg = "/home/user1/venvpython/images/winterbackground.jpg"
			if users_theme == 'Summer':
				pathtobackg = "/home/user1/venvpython/images/summerbackground.jpg"	
			if users_theme == 'Light':
				pathtobackg = "/home/user1/venvpython/images/lightbackground.jpg"
			if users_theme == 'Dark':
				pathtobackg = "/home/user1/venvpython/images/darkbackground.jpg"
			self.set_colors(users_colors)
				
		backg = ctk.CTkImage(light_image=Image.open(pathtobackg), dark_image=Image.open(pathtobackg), size=(s_width, s_height))
		Label_backg = ctk.CTkLabel(my_big_Frame, image=backg, text = "")
		Label_backg.place(x=0, y=0)
		Label_backg.focus_set()
		my_big_Frame.focus_set()
		my_big_Frame.focus_force()
						
		my_font = ctk.CTkFont(family="Arial", size=16, weight="bold", slant="roman", underline=False, overstrike=False)
		
		GPGButton = ctk.CTkButton(self, text="Home", text_color="white", border_width=2, border_color="white", fg_color=System_button_color, width=120, height=32, font=my_font, command=self.create_meny)
		GPGButton.place(relx=0.1, rely=0.1, anchor="center")
		
		if path_to_USB_secure == 'Secure USB folder is available':
			GPGButton = ctk.CTkButton(self, text="GPG", text_color="white", border_width=2, border_color="white", fg_color=GPG_button_color, width=120, height=32, font=my_font, command=self.create_GPGmeny)
			GPGButton.place(relx=0.2, rely=0.1, anchor="center")
			
			YubikeyButton = ctk.CTkButton(self, text="Yubikey", text_color="white", border_width=2, border_color="white", fg_color=Yubikey_button_color, width=120, height=32, font=my_font, command=self.create_Yubikeymeny)
			YubikeyButton.place(relx=0.3, rely=0.1, anchor="center")
			
			secusbButton = ctk.CTkButton(self, text="Secure archive", text_color="white", border_width=2, border_color="white", fg_color=SecUSB_button_color, width=120, height=32, font=my_font, command=self.create_SecUSBmeny)
			secusbButton.place(relx=0.4, rely=0.1, anchor="center")
			
			idButton = ctk.CTkButton(self, text="Digital ID", text_color="white", border_width=2, border_color="white", fg_color=DigitalID_button_color, width=120, height=32, font=my_font, command=self.create_DigitalIDmeny)
			idButton.place(relx=0.5, rely=0.1, anchor="center")
			
			boltcardButton = ctk.CTkButton(self, text="Boltcard", text_color="white", border_width=2, border_color="white", fg_color=Boltcard_button_color, width=120, height=32, font=my_font, command=self.create_Boltcardmeny)
			boltcardButton.place(relx=0.6, rely=0.1, anchor="center")
			
			HelpButton = ctk.CTkButton(self, text="Help", text_color="white", border_width=2, border_color="white", fg_color=Help_button_color, width=120, height=32, font=my_font, command=self.create_helpmeny)
			HelpButton.place(relx=0.93, rely=0.05, anchor="center")
			
			settimeButton = ctk.CTkButton(self, text="Settings", text_color="white", border_width=2, border_color="white", fg_color=System_button_color, width=120, height=32, font=my_font, command=self.create_getSettimetextbox)
			settimeButton.place(relx=0.93, rely=0.1, anchor="center")

		ExitButton = ctk.CTkButton(self, text="Close and exit", text_color="white", border_width=2, border_color="white", fg_color=System_button_color, width=120, height=32, font=my_font, command=self.encryptanddestroy)
		ExitButton.place(relx=0.5, rely=0.95, anchor="center")

		self.create_Hometextbox()
	
	def new_user_account_selection(self):
		# The smaller frame
		my_Frame = ctk.CTkFrame(self, 
		width=1200, 
		height=650,
		border_width=4,
		border_color="blue"
		)
		my_Frame.place(relx=0.5, rely=0.6, anchor="center")
		my_Frame.focus_set()
		my_Frame.focus_force()
		
		pathtobackg = "/home/user1/venvpython/images/bluebackground.jpg"
		backg = ctk.CTkImage(light_image=Image.open(pathtobackg), dark_image=Image.open(pathtobackg), size=(1200, 650))
		Label_backg = ctk.CTkLabel(my_Frame, image=backg, text = "")
		Label_backg.place(x=0, y=0)
		my_font = ctk.CTkFont(family="Arial", size=18, weight="bold", slant="roman", underline=False, overstrike=False)
		
		if path_to_USB_secure == 'Secure USB folder is not available':
			Button8 = ctk.CTkButton(my_Frame, text="Create a new account and one extra key for external communication (Recommended)", text_color="white", fg_color="blue", border_width=2, border_color="white", height=40, font=my_font, command=self.create_getStartedmeny)
			Button8.place(relx=0.5, rely=0.3, anchor="center")
			Button7 = ctk.CTkButton(my_Frame, text="Create only a new account", text_color="white", fg_color="blue", border_width=2, border_color="white", font=my_font, command=self.new_secureUSB)
			Button7.place(relx=0.5, rely=0.6, anchor="center")
		else:
			Label1 = ctk.CTkLabel(my_Frame, text="You are already logged in.", text_color="white", fg_color="black", font=my_font)
			Label1.place(relx=0.44, rely=0.4, anchor="e")
			Label11 = ctk.CTkLabel(my_Frame, text=PersonalGPGKey, text_color="white", fg_color="black", font=my_font)
			Label11.place(relx=0.45, rely=0.4, anchor="w")
			
	def create_getStartedmeny(self):
		global s_width,s_height
		#The big frame
		my_big_Frame = ctk.CTkFrame(self, 
		width=s_width, 
		height=s_height,
		border_width=1,
		border_color="blue"
		)
		my_big_Frame.place(relx=0.5, rely=0.5, anchor="center")
		
		pathtobackg = "/home/user1/venvpython/images/blue.jpg"
		backg = ctk.CTkImage(light_image=Image.open(pathtobackg), dark_image=Image.open(pathtobackg), size=(s_width, s_height))
		Label_backg = ctk.CTkLabel(my_big_Frame, image=backg, text = "")
		Label_backg.place(x=0, y=0)
		my_big_Frame.focus_set()
		my_big_Frame.focus_force()

		my_font = ctk.CTkFont(family="Arial", size=16, weight="bold", slant="roman", underline=False, overstrike=False)
		
		GPGButton = ctk.CTkButton(self, text="Home", text_color="white", border_width=2, border_color="white", fg_color="blue", font=my_font, command=self.create_meny)
		GPGButton.place(relx=0.1, rely=0.1, anchor="center")
		
		HelpButton = ctk.CTkButton(self, text="Help", text_color="white", border_width=2, border_color="white", fg_color="orange", width=120, height=32, font=my_font, command=self.create_helpmeny)
		HelpButton.place(relx=0.93, rely=0.05, anchor="center")
		
		settimeButton = ctk.CTkButton(self, text="Settings", text_color="white", border_width=2, border_color="white", fg_color="blue", width=120, height=32, font=my_font, command=self.create_getSettimetextbox)
		settimeButton.place(relx=0.93, rely=0.1, anchor="center")
		
		ExitButton = ctk.CTkButton(self, text="Close and exit", text_color="white", border_width=2, border_color="white", fg_color="blue", width=120, height=32, font=my_font, command=self.encryptanddestroy)
		ExitButton.place(relx=0.5, rely=0.95, anchor="center")
		
		# The smaller frame
		my_Frame = ctk.CTkFrame(self, 
		width=1200, 
		height=650,
		border_width=4,
		border_color="blue"
		)
		my_Frame.place(relx=0.5, rely=0.6, anchor="center")
		
		pathtobackg = "/home/user1/venvpython/images/bluebackground.jpg"
		backg = ctk.CTkImage(light_image=Image.open(pathtobackg), dark_image=Image.open(pathtobackg), size=(1200, 650))
		Label_backg = ctk.CTkLabel(my_Frame, image=backg, text = "")
		Label_backg.place(x=0, y=0)

		my_font = ctk.CTkFont(family="Arial", size=20, weight="bold", slant="italic", underline=True, overstrike=False)
		my_font = ctk.CTkFont(family="Arial", size=20, weight="bold", slant="italic", underline=True, overstrike=False)
		
		Label2 = ctk.CTkLabel(self, text="This will let you set-up:", text_color="white", fg_color="black", font=my_font)
		Label2.place(relx=0.5, rely=0.38, anchor="center")
		my_font = ctk.CTkFont(family="Arial", size=16, weight="bold", slant="italic", underline=True, overstrike=False)
		Label23 = ctk.CTkLabel(self, text="(1). An encryption key for safe, and private, communication that can be used with emails etc.", text_color="white", fg_color="black", font=my_font)
		Label23.place(relx=0.5, rely=0.44, anchor="center")
		my_font = ctk.CTkFont(family="Arial", size=16, weight="bold", slant="italic", underline=True, overstrike=False)
		Label4 = ctk.CTkLabel(self, text="(2). An encrypted archive for important files, passwords and bitcoin wallets etc.", text_color="white", fg_color="black", font=my_font)
		Label4.place(relx=0.5, rely=0.49, anchor="center")
		Label5 = ctk.CTkLabel(self, text="(3). A secondary backup on a USB-stick in case of breakage, fire or theft.", text_color="white", fg_color="black", font=my_font)
		Label5.place(relx=0.5, rely=0.54, anchor="center")
		my_font = ctk.CTkFont(family="Arial", size=14, weight="bold", slant="roman", underline=False, overstrike=False)
		Label6 = ctk.CTkLabel(self, text="(You will need a USB-stick ready to connect when instructed during the setup process.)", text_color="white", fg_color="black", font=my_font)
		Label6.place(relx=0.5, rely=0.58, anchor="center")
		my_font = ctk.CTkFont(family="Arial", size=16, weight="bold", slant="italic", underline=True, overstrike=False)
		Label7 = ctk.CTkLabel(self, text="(4). A Yubikey 5 NFC (hardware device) with subkeys for encrypting emails on computers and smartphones (optional).", text_color="white", fg_color="black", font=my_font)
		Label7.place(relx=0.5, rely=0.63, anchor="center")
		my_font = ctk.CTkFont(family="Arial", size=16, weight="bold", slant="roman", underline=False, overstrike=False)
		
		Button3 = ctk.CTkButton(self, text="Got it. Lets Go!", text_color="black", fg_color="pink", border_width=2, border_color="white", font=my_font, command=self.create_getStartedmeny_Pre)
		Button3.place(relx=0.5, rely=0.7, anchor="center")
	
	def create_getStartedmeny_Pre(self):
		# Make sure time and date is correct before creating anyuy new keys 
		global filepathdestinationfolder
		global SecUSB_button_color
			
		my_Frame = ctk.CTkFrame(self, 
		width=1200, 
		height=650,
		border_width=4,
		border_color="blue"
		)
		my_Frame.place(relx=0.5, rely=0.6, anchor="center")
		pathtobackg = "/home/user1/venvpython/images/bluebackground.jpg"
		
		backg = ctk.CTkImage(light_image=Image.open(pathtobackg), dark_image=Image.open(pathtobackg), size=(1200, 650))
		Label_backg = ctk.CTkLabel(my_Frame, image=backg, text = "")
		Label_backg.place(x=0, y=0)
		
		my_Frame.focus_set()
		my_Frame.focus_force()			
		
		def do_create_getStartedmeny_Pre():
			global filepathdestinationfolder
			key_fingerprint = ''
			# Set the date and time
			thedate = cal.get_date()
			thetime = time_picker.time()
			
			thedatestr = str('sudo date -s \'' + str(thedate) + ' ' + str(thetime[0]) + ':' + str(thetime[1]) + ':00\'')			
			os.system(thedatestr)
			thestr = 'sudo hwclock -w'	
			os.system(thestr)
			os.system(thestr)
			self.create_getStartedmeny2()
			
		gpg = gnupg.GPG(gnupghome='/home/user1/.gnupg/')
		
		my_font = ctk.CTkFont(family="Arial", size=22, weight="bold", slant="roman", underline=True, overstrike=False)
		
		Label1 = ctk.CTkLabel(my_Frame, text="Important! Before creating new account make sure the time and date are correct:", text_color="white", fg_color="black", font=my_font)
		Label1.place(relx=0.5, rely=0.1, anchor="center")
		
		time_picker = AnalogPicker(my_Frame, type=constants.HOURS24)
		time_picker.setHours(datetime.now().hour)
		time_picker.setMinutes(datetime.now().minute)
		time_picker.place(relx=0.65, rely=0.45, anchor="e")
		
		theme = AnalogThemes(time_picker)
		theme.setNavyBlue()
		time_picker.configAnalog(textcolor="#ffffff", bg="#0a0832", bdColor="#000000", headbdcolor="#000000")
		
		cal = DateEntry(my_Frame, width=20, text_color="white", bg="darkblue", fg="black", year=2024)
		cal.place(relx=0.65, rely=0.73, anchor="e")
			
		Button = ctk.CTkButton(my_Frame, text="Next!", text_color="white", fg_color=SecUSB_button_color, border_width=2, border_color="white", font=my_font, command=do_create_getStartedmeny_Pre)
		Button.place(relx=0.5, rely=0.86, anchor="center")
		
	def create_getStartedmeny2(self):	
		global path_to_USB_secure
		global filepathdestinationfolder
		global commkey
		check_var = ctk.StringVar(value="off") 
		pathtobackg = "/home/user1/venvpython/images/bluebackground.jpg"
		
		my_font = ctk.CTkFont(family="Arial", size=20, weight="bold", slant="italic", underline=True, overstrike=False)
		
		my_Frame = ctk.CTkFrame(self, 
		width=1200, 
		height=650,
		border_width=4,
		border_color="blue"
		)
		my_Frame.place(relx=0.5, rely=0.6, anchor="center")
		
		backg = ctk.CTkImage(light_image=Image.open(pathtobackg), dark_image=Image.open(pathtobackg), size=(1200, 650))
		Label_backg = ctk.CTkLabel(my_Frame, image=backg, text = "")
		Label_backg.place(x=0, y=0)
		my_Frame.focus_set()
		my_Frame.focus_force()
		
		def tPassphrase():
			if Secret_passphrasePrivateEntry.cget('show') == '':
				Secret_passphrasePrivateEntry.configure(show='*')
			else:
				Secret_passphrasePrivateEntry.configure(show='')
		def t2Passphrase():
			if Secret_passphraseCommunicationEntry.cget('show') == '':
				Secret_passphraseCommunicationEntry.configure(show='*')
			else:
				Secret_passphraseCommunicationEntry.configure(show='')
		
		def tPIN():
			if Secret_PIN.cget('show') == '':
				Secret_PIN.configure(show='*')
			else:
				Secret_PIN.configure(show='')
		
		def tAdminPIN():
			if Secret_AdminPIN.cget('show') == '':
				Secret_AdminPIN.configure(show='*')
			else:
				Secret_AdminPIN.configure(show='')
		
		def getStarted():
			global path_to_USB_secure
			global PersonalGPGKey
			global filepathdestinationfolder
			global commkey
			gpg = gnupg.GPG(gnupghome='/home/user1/.gnupg/')

			backg = ctk.CTkImage(light_image=Image.open(pathtobackg), dark_image=Image.open(pathtobackg), size=(1200, 650))
			Label_backg = ctk.CTkLabel(my_Frame, image=backg, text = "")
			Label_backg.place(x=0, y=0)	
			my_Frame.focus_set()
			my_Frame.focus_force()
				
			# Create a GPG master key for personal use, namePrivateEntry emailPrivateEntry Secret_passphrasePrivateEntry
			input_data_priv = gpg.gen_key_input(key_type='rsa', name_real=namePrivateEntry.get(), expire_date='0', key_length='4096', name_email=emailPrivateEntry.get(), passphrase=Secret_passphrasePrivateEntry.get())
			privatekey = gpg.gen_key(input_data_priv)
			
			# Create a GPG master key for communication and three subkeys, nameCommunicationEntry emailCommunicationEntry Secret_passphraseCommunicationEntry
			input_data_comm = gpg.gen_key_input(key_type='rsa',  key_usage='sign', name_real=nameCommunicationEntry.get(), expire_date='0', key_length='4096', name_email=emailCommunicationEntry.get(), passphrase=Secret_passphraseCommunicationEntry.get())
			communicationkey = gpg.gen_key(input_data_comm)
			
			PersonalGPGKey = str(privatekey.fingerprint)
			commkey = str(communicationkey.fingerprint)	
			
			key = gpg.add_subkey(commkey, algorithm='rsa4096', usage='sign', expire='3y')
			key = gpg.add_subkey(commkey, algorithm='rsa4096', usage='encrypt', expire='3y')
			key = gpg.add_subkey(commkey, algorithm='rsa4096', usage='auth', expire='3y')
			
			# Create a Secure folder
			full_path = str(filepathdestinationfolder) + "/secure/"
			full_path_wallets = str(filepathdestinationfolder) + "/secure/wallets/"
			full_path_keys = str(filepathdestinationfolder) + "/secure/keys/"
			full_path_paperwallets = str(filepathdestinationfolder) + "/secure/wallets/paperwallets/"
			full_path_settings_file = str(filepathdestinationfolder) + "/secure/settings.csv"
			full_path_paperwallets_file = str(filepathdestinationfolder) + "/secure/wallets/paperwallets/paperwallets.csv"
			full_path_boltcards = str(filepathdestinationfolder) + "/secure/boltcards/"
			full_path_boltcards_file = str(filepathdestinationfolder) + "/secure/boltcards/boltcards.csv"
			full_path_FIDOKeys = str(filepathdestinationfolder) + "/secure/FIDO/"
			full_path_FIDOKeys_file = str(filepathdestinationfolder) + "/secure/FIDO/FIDOKeys.csv"
			full_path_IDs = str(filepathdestinationfolder) + "/secure/ID/"
			full_path_IDs_file = str(filepathdestinationfolder) + "/secure/ID/IDs.csv"
			
			os.makedirs(os.path.dirname(full_path))
			os.makedirs(os.path.dirname(full_path_wallets))
			os.makedirs(os.path.dirname(full_path_keys))
			os.makedirs(os.path.dirname(full_path_paperwallets))
			os.makedirs(os.path.dirname(full_path_boltcards))
			os.makedirs(os.path.dirname(full_path_FIDOKeys))
			os.makedirs(os.path.dirname(full_path_IDs))
			
			c = open(full_path + "passwords.txt", 'w')
			c.write(str("Passwords\n___________________________________\n\nYubikey\n\n   FIDO PIN:  \n\n   OpenPGP Admin PIN:  \n\n   OpenPGP PIN:  \n\n   Comment:  \n\n___________________________________\n\nUser/account: \n\n   Password: \n\n   Comment: \n\n___________________________________\n\nUser/account: \n\n   Password: \n\n   Comment: \n\n___________________________________\n"))
			c.close()
			c = open(full_path_wallets + "wallets.txt", 'w')
			c.write(str("Wallets\n___________________________________\n\nName: \n\n   Seed words/key: \n\n   Comment: \n\n___________________________________\n\nName: \n\n   Seed words/key: \n\n   Comment: \n"))
			c.close()
			with open(full_path_settings_file, 'w', newline='') as file:
				writer = csv.writer(file)
				field = ['Username', 'Theme', 'Colors']
			with open(full_path_paperwallets_file, 'w', newline='') as file:
				writer = csv.writer(file)
				field = ['Name', 'Datecreated', 'Pubkey', 'wif', 'mnemonic', 'amount']
			with open(full_path_boltcards_file, 'w', newline='') as file:
				writer = csv.writer(file)
				field = ['name', 'description', 'datecreated', 'LNURLaddress', 'resetcode', 'programmingcode', 'withdrawallimit', 'dailywithdrawallimit', 'LNHublink', 'LNHubuser', 'LNHubuserpassword']	
			with open(full_path_FIDOKeys_file, 'w', newline='') as file:
				writer = csv.writer(file)
				field = ['name', 'description', 'services']	
			with open(full_path_IDs_file, 'w', newline='') as file:
				writer = csv.writer(file)
				field = ['type', 'fingerprint', 'name', 'lastname', 'address', 'address2', 'birthdate', 'sex', 'issuedate']
									
			path_to_USB_secure = 'Secure USB folder is available'
			
			# Make initial settings in settings file
			with open(full_path_settings_file, 'w') as result:
				csvwriter = csv.writer(result)
				new_settings = [
								namePrivateEntry.get(),
								'Winter',
								'Varied']
				csvwriter.writerow(new_settings)					
					
			# Backup both master keys (communication key is still with subkeys intact).
			privatekeyfilename = 'privateKey' + PersonalGPGKey + ".gpg"
			communicationkeyfilename = 'privateKey' + commkey + ".gpg"
			full_path_private = filepathdestinationfolder + "/" + privatekeyfilename
			full_path_communication = filepathdestinationfolder + "/secure/keys/" + communicationkeyfilename
			
			# Export the private key and write to file in /home/user1 and to /home/user1/secure/keys
			ascii_armored_private_key = gpg.export_keys(PersonalGPGKey, True, expect_passphrase=False)
			f2 = open(full_path_private, 'w')
			f2.write(ascii_armored_private_key)
			f2.close()
			destPriv = filepathdestinationfolder + "/secure/keys/" + privatekeyfilename
			shutil.copy(full_path_private, destPriv)
			
			# Export the communication key and write to file in /secure/keys
			ascii_armored_communication_key = gpg.export_keys(commkey, True, expect_passphrase=False)
			f2 = open(full_path_communication, 'w')
			f2.write(ascii_armored_communication_key)
			f2.close()
			
			# Export the communication subkeys and write to file in /secure/keys
			communicationsubkeyfilename = 'allsubKeys' + commkey + ".gpg"
			cmd = 'gpg --armor --export-secret-subkeys ' + commkey + ' > ' + filepathdestinationfolder + '/secure/keys/' + communicationsubkeyfilename
			os.system(cmd)
			
			# Encrypt the secure folder and place on the USB-stick. Then ask user to remove the USB-stick
			full_path = str(filepathdestinationfolder) + "/secure/"
			compressed_file = shutil.make_archive(full_path, 'gztar', full_path)
			
			# Encrypt the tarfile and remove the unencrypted tarfile
			encrypted_data = gpg.encrypt_file(compressed_file, PersonalGPGKey, always_trust=True) 
			
			cmd = 'shred -zu -n7 ' + filepathdestinationfolder + "/" + "secure.tar.gz"
			os.system(cmd)
			# Write the encrypted file to the offline device /home/user1
			compressedoutfile = open(filepathdestinationfolder + "/" + PersonalGPGKey + 'securefolder.tar.gz.gpg', 'w')
			compressedoutfile.write(str(encrypted_data))
			compressedoutfile.close()

			full_path = filepathdestinationfolder + "/" + PersonalGPGKey + 'securefolder.tar.gz.gpg'
			path_to_USB_secure = 'Secure USB folder is available'
			timeSecUSBLastModified = str(time.ctime(os.path.getmtime(full_path)))
			
			# Copy the exported private key to a USB-device
			messagebox.showinfo("Information", "Insert a USB-device (for making a backup) and double-click to select it.")
			time.sleep(4)
			localfilepathdestinationfolder = filedialog.askdirectory(initialdir='/media/user1/')
			shutil.copy(full_path_private, localfilepathdestinationfolder)
			
			# Write the encrypted file to second USB-stick
			compressedoutfile = open(localfilepathdestinationfolder + "/" + PersonalGPGKey + 'securefolder.tar.gz.gpg', 'w')
			compressedoutfile.write(str(encrypted_data))
			compressedoutfile.close()
			messagebox.showinfo("Information", "Encrypted files and keys written to the USB-device successfully. Please remove USB-device.")
			
			# Set Admin PIN, PIN, name, email on Yubikey if checkbox is set. Secret_PIN Secret_AdminPIN (and name/email as in Communication key)
			if checkbox.get() == "on":
				tk.messagebox.showinfo('Information', 'Connect the Yubikey')
				
				backg = ctk.CTkImage(light_image=Image.open(pathtobackg), dark_image=Image.open(pathtobackg), size=(1200, 650))
				Label_backg = ctk.CTkLabel(my_Frame, image=backg, text = "")
				Label_backg.place(x=0, y=0)
				my_font = ctk.CTkFont(family="Tahoma", size=20, weight="bold", slant="roman", underline=False, overstrike=False)
				
				Label = ctk.CTkLabel(my_Frame, text='In the terminal window that will open:\n_________________________\n1. Type \"admin\" and hit enter to toggle until it says \"admin commands are allowed\"\n2. Type \"passwd\" hit enter.\nSelect \"3\" and hit enter.\n        Enter current admin PIN (default admin PIN is 12345678).\n      Add new admin PIN (min 8 digits).\n        Confirm the new admin PIN.\n3. Select \"1\" and hit enter.\n      Enter current PIN (default PIN is 123456).\n      Add new PIN (min 6 digits).\n        Confirm new PIN.\n4. Type \"q\" and hit enter.\n5. Type \"quit\" and hit enter.\n6. Exit the terminal by typing \"exit\" and hit enter.', text_color="white", fg_color="black", font=my_font)
				Label.place(relx=0.5, rely=0.35, anchor="center")
				my_Frame.focus_set()
				my_Frame.focus_force()
				
				time.sleep(1)

				goButton = ctk.CTkButton(my_Frame, text="Start", text_color="black", fg_color="pink", border_width=2, border_color="white", font=my_font, command=next_step)
				goButton.place(relx=0.5, rely=0.8, anchor="center")

			else:
				get_started_without_Yubikey_finished()
		
		def get_started_without_Yubikey_finished():
			backg = ctk.CTkImage(light_image=Image.open(pathtobackg), dark_image=Image.open(pathtobackg), size=(1200, 650))
			Label_backg = ctk.CTkLabel(my_Frame, image=backg, text = "")
			Label_backg.place(x=0, y=0)
			my_font = ctk.CTkFont(family="Tahoma", size=18, slant="roman", underline=False, overstrike=False)
			
			my_Frame.focus_set()
			my_Frame.focus_force()

			goButton = ctk.CTkButton(my_Frame, text="Click to complete the setup", text_color="black", fg_color="pink", border_width=2, border_color="white", font=my_font, command=self.getStartedfinnished)
			goButton.place(relx=0.5, rely=0.35, anchor="center")
			
		def next_step():
			command= 'gpg --card-edit'
			os.system("lxterminal -e 'bash -c \""+command+";bash\"'")
			backg = ctk.CTkImage(light_image=Image.open(pathtobackg), dark_image=Image.open(pathtobackg), size=(1200, 650))
			Label_backg = ctk.CTkLabel(my_Frame, image=backg, text = "")
			Label_backg.place(x=0, y=0)
			my_font = ctk.CTkFont(family="Tahoma", size=20, weight="bold", slant="roman", underline=False, overstrike=False)
			
			Label = ctk.CTkLabel(my_Frame, text='In the terminal window that will open:\n_________________________\n1. Type \"admin\" and hit enter to toggle until it says \"admin commands are allowed\"\n2. Type \"passwd\" hit enter.\nSelect \"3\" and hit enter.\n        Enter current admin PIN (default admin PIN is 12345678).\n      Add new admin PIN (min 8 digits).\n        Confirm the new admin PIN.\n3. Select \"1\" and hit enter.\n      Enter current PIN (default PIN is 123456).\n      Add new PIN (min 6 digits).\n        Confirm new PIN.\n4. Type \"q\" and hit enter.\n5. Type \"quit\" and hit enter.\n6. Exit the terminal by typing \"exit\" and hit enter.', text_color="white", fg_color="black", font=my_font)
			Label.place(relx=0.5, rely=0.35, anchor="center")
			
			goButton = ctk.CTkButton(my_Frame, text="Next", text_color="black", fg_color="pink", border_width=2, border_color="white", font=my_font, command=next_step2)
			goButton.place(relx=0.5, rely=0.8, anchor="center")
		
		def next_step2():
			backg = ctk.CTkImage(light_image=Image.open(pathtobackg), dark_image=Image.open(pathtobackg), size=(1200, 650))
			Label_backg = ctk.CTkLabel(my_Frame, image=backg, text = "")
			Label_backg.place(x=0, y=0)
			my_font = ctk.CTkFont(family="Tahoma", size=20, weight="bold", slant="roman", underline=False, overstrike=False)
			Label = ctk.CTkLabel(my_Frame, text='In the terminal window that will open:\n_________________________\nType "toggle" and hit enter.\n2.Type "key 1" and "key 2" etc to toggle select/deselect subkey.\n        Selected subkey will be marked with "*"\n        Make sure only ONE subkey is selected before moving on to next step.\n3. Type "keytocard" to move the selected subkey to the Yubikey.\nIf the subkey is marked with \"usage: S\" then select \"(1) Signature key\".\nDeselect the \"Key 1\" by typing \"Key 1\" one more time.\n4. Repeat with all three subkeys.\n5. Type "save" and hit enter.\n6. Type "exit" and hit enter.', text_color="white", fg_color="black", font=my_font)
			Label.place(relx=0.5, rely=0.2, anchor="center")
			
			goButton = ctk.CTkButton(my_Frame, text="Start", text_color="black", fg_color="pink", border_width=2, border_color="white", font=my_font, command=next_step3)
			goButton.place(relx=0.5, rely=0.8, anchor="center")
				
			
		def next_step3():
			command= 'gpg --edit-key ' + commkey
			os.system("lxterminal -e 'bash -c \""+command+";bash\"'")
			backg = ctk.CTkImage(light_image=Image.open(pathtobackg), dark_image=Image.open(pathtobackg), size=(1200, 650))
			Label_backg = ctk.CTkLabel(my_Frame, image=backg, text = "")
			Label_backg.place(x=0, y=0)
			my_font = ctk.CTkFont(family="Tahoma", size=20, weight="bold", slant="roman", underline=False, overstrike=False)
			Label = ctk.CTkLabel(my_Frame, text='In the terminal window that will open:\n_________________________\nType "toggle" and hit enter.\n2.Type "key 1" and "key 2" etc to toggle select/deselect subkey.\n        Selected subkey will be marked with "*"\n        Make sure only ONE subkey is selected before moving on to next step.\n3. Type "keytocard" to move the selected subkey to the Yubikey.\nIf the subkey is marked with \"usage: S\" then select \"(1) Signature key\".\nDeselect the \"Key 1\" by typing \"Key 1\" one more time.\n4. Repeat with all three subkeys.\n5. Type "save" and hit enter.\n6. Type "exit" and hit enter.', text_color="white", fg_color="black", font=my_font)
			Label.place(relx=0.5, rely=0.2, anchor="center")
			
			goButton = ctk.CTkButton(my_Frame, text="Next", text_color="black", fg_color="pink", border_width=2, border_color="white", font=my_font, command=next_step4)
			goButton.place(relx=0.5, rely=0.8, anchor="center")
			
		def next_step4():
			global commkey
			global filepathdestinationfolder
			gpg = gnupg.GPG(gnupghome='/home/user1/.gnupg/')
			
			backg = ctk.CTkImage(light_image=Image.open(pathtobackg), dark_image=Image.open(pathtobackg), size=(1200, 650))
			Label_backg = ctk.CTkLabel(my_Frame, image=backg, text = "")
			Label_backg.place(x=0, y=0)
			my_font = ctk.CTkFont(family="Tahoma", size=20, weight="bold", slant="roman", underline=False, overstrike=False)
			
			# Delete the Communication key (with snubbed subkeys) and import it from secure archive (to get working subkeys again)
			try:
				key = gpg.delete_keys(commkey, True, expect_passphrase=False)  #passphrase=USER_INP)
			except ValueError as ve:
				messagebox.showinfo('Information', 'Something went wrong.')
					
			communicationkeyfilename = 'privateKey' + commkey + ".gpg"
			full_path_communication = filepathdestinationfolder + "/secure/keys/" + communicationkeyfilename
			
			import_result = gpg.import_keys_file(full_path_communication)

			goButton = ctk.CTkButton(my_Frame, text="Click to complete the setup", text_color="black", fg_color="pink", border_width=2, border_color="white", font=my_font, command=self.getStartedfinnished)
			goButton.place(relx=0.5, rely=0.4, anchor="center")
			
		my_font = ctk.CTkFont(family="Tahoma", size=34, weight="bold", slant="roman", underline=True, overstrike=False)
		
		Label = ctk.CTkLabel(my_Frame, text="Please provide your data:", text_color="white", fg_color="black", font=my_font)
		Label.place(relx=0.3, rely=0.1, anchor="w")
		my_font = ctk.CTkFont(family="Arial", size=16, slant="roman", underline=False, overstrike=False)
		# Data for the private key
		Labelprivate = ctk.CTkLabel(my_Frame, text="Private key*:", text_color="white", fg_color="black", font=my_font)
		Labelprivate.place(relx=0.3, rely=0.17, anchor="w")
		namePrivate = ctk.CTkLabel(my_Frame, text="Full name:", text_color="white", fg_color="black", font=my_font)
		namePrivate.place(relx=0.34, rely=0.22, anchor="e")
		namePrivateEntry = ctk.CTkEntry(my_Frame, placeholder_text="Bob Smith", width=320, height=25, text_color="white", border_color="white", border_width=3, corner_radius=8, font=my_font)
		namePrivateEntry.place(relx=0.35, rely=0.22, anchor="w")
		
		Label2 = ctk.CTkLabel(my_Frame, text="Email:", text_color="white", fg_color="black", font=my_font)
		Label2.place(relx=0.34, rely=0.27, anchor="e")
		emailPrivateEntry = ctk.CTkEntry(my_Frame, placeholder_text="bob.smith@cyb.org", width=320, height=25, text_color="white", border_color="white", border_width=3, corner_radius=8, font=my_font)
		emailPrivateEntry.place(relx=0.35, rely=0.27, anchor="w")
		
		LabelPassphrasePrivate = ctk.CTkLabel(my_Frame, text="Secret passphrase:", text_color="white", fg_color="black", font=my_font)
		LabelPassphrasePrivate.place(relx=0.34, rely=0.32, anchor="e")
		Secret_passphrasePrivateEntry = ctk.CTkEntry(my_Frame, placeholder_text="*****************", show='*', width=320, height=25, text_color="white", border_color="white", border_width=3, corner_radius=8, font=my_font)
		Secret_passphrasePrivateEntry.place(relx=0.35, rely=0.32, anchor="w")
		tButton = ctk.CTkButton(my_Frame, text="Show/hide passphrase", text_color="black", fg_color="pink", border_width=2, border_color="white", font=my_font, command=tPassphrase)
		tButton.place(relx=0.7, rely=0.32, anchor="center")
		
		# Data for the communication key
		Labelcomm = ctk.CTkLabel(my_Frame, text="Communication key**:", text_color="white", fg_color="black", font=my_font)
		Labelcomm.place(relx=0.28, rely=0.37, anchor="w")
		Label11 = ctk.CTkLabel(my_Frame, text="Full name:", text_color="white", fg_color="black", font=my_font)
		Label11.place(relx=0.34, rely=0.42, anchor="e")
		nameCommunicationEntry = ctk.CTkEntry(my_Frame, placeholder_text="Carl Smitty", width=320, height=25, text_color="white", border_color="white", border_width=3, corner_radius=8, font=my_font)
		nameCommunicationEntry.place(relx=0.35, rely=0.42, anchor="w")
		
		Label22 = ctk.CTkLabel(my_Frame, text="Email:", text_color="white", fg_color="black", font=my_font)
		Label22.place(relx=0.34, rely=0.47, anchor="e")
		emailCommunicationEntry = ctk.CTkEntry(my_Frame, placeholder_text="Carl.smitty@thecave.net", width=320, height=25, text_color="white", border_color="white", border_width=3, corner_radius=8, font=my_font)
		emailCommunicationEntry.place(relx=0.35, rely=0.47, anchor="w")
		
		LabelPassphraseComm = ctk.CTkLabel(my_Frame, text="Secret passphrase:", text_color="white", fg_color="black", font=my_font)
		LabelPassphraseComm.place(relx=0.34, rely=0.52, anchor="e")
		Secret_passphraseCommunicationEntry = ctk.CTkEntry(my_Frame, placeholder_text="*****************", show='*', width=320, height=25, text_color="white", border_color="white", border_width=3, corner_radius=8, font=my_font)
		Secret_passphraseCommunicationEntry.place(relx=0.35, rely=0.52, anchor="w")
		tButton2 = ctk.CTkButton(my_Frame, text="Show/hide passphrase", text_color="black", fg_color="pink", border_width=2, border_color="white", font=my_font, command=t2Passphrase)
		tButton2.place(relx=0.7, rely=0.52, anchor="center")
		
		checkbox = ctk.CTkCheckBox(my_Frame, text="I got a Yubikey 5 NFC.", variable=check_var, onvalue="on", offvalue="off", text_color="white", fg_color="black", font=my_font)
		checkbox.place(relx=0.35, rely=0.58, anchor="w")
		
		goButton = ctk.CTkButton(my_Frame, text="Lets Go! ***", text_color="black", fg_color="pink", border_width=2, border_color="white", font=my_font, command=getStarted)
		goButton.place(relx=0.5, rely=0.66, anchor="center")
		my_font = ctk.CTkFont(family="Arial", size=16, weight="bold", slant="roman", underline=False, overstrike=False)
		LLabel3 = ctk.CTkLabel(my_Frame, text="*** This can take a while.. Move mouse around to create randomness...\nFollow all the instructions for the rest of the setup.", text_color="white", fg_color="black", font=my_font)
		LLabel3.place(relx=0.5, rely=0.73, anchor="center")
		my_font = ctk.CTkFont(family="Helvetica", size=15, weight="normal", slant="roman", underline=False, overstrike=False)
		Labelinf1 = ctk.CTkLabel(my_Frame, text="* Private key is for private use (like encrypting the secure archive on the offline device etc).", text_color="white", fg_color="black", font=my_font)
		Labelinf1.place(relx=0.05, rely=0.81, anchor="w")
		Labelinf2 = ctk.CTkLabel(my_Frame, text="** Communication key is used for signing other public keys, encrypting emails etc. Subkeys should be on a Yubikey (for safe use with computers/smartphones).", text_color="white", fg_color="black", font=my_font)
		Labelinf2.place(relx=0.05, rely=0.87, anchor="w")
			
	def getStartedfinnished(self):
		my_Frame = ctk.CTkFrame(self, 
		width=1200, 
		height=650,
		border_width=4,
		border_color="blue"
		)
		my_Frame.place(relx=0.5, rely=0.6, anchor="center")
		
		pathtobackg = "/home/user1/venvpython/images/bluebackground.jpg"

		backg = ctk.CTkImage(light_image=Image.open(pathtobackg), dark_image=Image.open(pathtobackg), size=(1200, 650))
		Label_backg = ctk.CTkLabel(my_Frame, image=backg, text = "")
		Label_backg.place(x=0, y=0)
		
		# Output what has been done from getStarted
		my_font = ctk.CTkFont(family="Arial", size=24, weight="bold", slant="italic", underline=True, overstrike=False)
		Label2 = ctk.CTkLabel(my_Frame, text="Finished!", text_color="white", fg_color="black", font=my_font)
		Label2.place(relx=0.5, rely=0.3, anchor="center")
		
		my_font = ctk.CTkFont(family="Arial", size=16, weight="bold", slant="italic", underline=True, overstrike=False)
		Label23 = ctk.CTkLabel(my_Frame, text="You have sucessfully created:", text_color="white", fg_color="black", font=my_font)
		Label23.place(relx=0.5, rely=0.37, anchor="center")
		
		my_font = ctk.CTkFont(family="Arial", size=16, weight="bold", slant="roman", underline=False, overstrike=False)
		Label3 = ctk.CTkLabel(my_Frame, text="(1). Two encryption keys that are placed on the offline device (this device). One for securing this device and one for external communication *.", text_color="white", fg_color="black", font=my_font)
		Label3.place(relx=0.5, rely=0.42, anchor="center")
		
		my_font = ctk.CTkFont(family="Arial", size=16, weight="bold", slant="italic", underline=False, overstrike=False)
		Label4 = ctk.CTkLabel(my_Frame, text="(2). An encrypted archive that can be used to storing files, passwords and bitcoin wallets etc.", text_color="white", fg_color="black", font=my_font)
		Label4.place(relx=0.5, rely=0.47, anchor="center")
		Label5 = ctk.CTkLabel(my_Frame, text="(3). A backup USB-stick in case the offline device breaks or there is a fire or theft etc.", text_color="white", fg_color="black", font=my_font)
		Label5.place(relx=0.5, rely=0.52, anchor="center")

		Label6 = ctk.CTkLabel(my_Frame, text="(4). A Yubikey 5 NFC (hardware device) with subkeys for encrypting emails on a smartphones etc (optional).", text_color="white", fg_color="black", font=my_font)
		Label6.place(relx=0.5, rely=0.57, anchor="center")
		my_font = ctk.CTkFont(family="Arial", size=16, weight="bold", slant="roman", underline=False, overstrike=False)
		
		Button3 = ctk.CTkButton(my_Frame, text="Start using the offline device", text_color="black", fg_color="pink", border_width=2, border_color="white", font=my_font, command=self.create_meny)
		Button3.place(relx=0.5, rely=0.7, anchor="center")
		my_font = ctk.CTkFont(family="Arial", size=14, slant="roman", underline=False, overstrike=False)
		
		Label7 = ctk.CTkLabel(my_Frame, text="* This key has been split into many parts. A master key  (to remain offline), a public key and three subkeys, to move to other devices.", text_color="white", fg_color="black", font=my_font)
		Label7.place(relx=0.5, rely=0.82, anchor="center")
		 
	def create_helpmeny(self):
		global Help_button_color
		self.create_abouthelptextbox()
		my_font = ctk.CTkFont(family="Arial", size=16, weight="bold", slant="roman", underline=False, overstrike=False)
		
		mainHelpButton = ctk.CTkButton(self, text="Help", text_color="white", border_width=2, border_color="white", fg_color="orange",  width=120, height=32, font=my_font, command=self.create_helpmeny)
		mainHelpButton.place(relx=0.93, rely=0.05, anchor="center")
		
		Button1 = ctk.CTkButton(self, text="Getting started", text_color="white", fg_color="orange", border_width=2, border_color="white", width=170, height=32, font=my_font, command=self.create_abouthelptextbox)
		Button1.place(relx=0.1, rely=0.2, anchor="center")
		
		Button2 = ctk.CTkButton(self, text="GPG", text_color="white", fg_color="orange", border_width=2, border_color="white", width=170, height=32, font=my_font, command=self.create_gpghelptextbox)
		Button2.place(relx=0.25, rely=0.2, anchor="center")
		
		Button3 = ctk.CTkButton(self, text="Yubikey", text_color="white", fg_color="orange", border_width=2, border_color="white", width=170, height=32, font=my_font, command=self.create_yubikeyhelptextbox)
		Button3.place(relx=0.4, rely=0.2, anchor="center")
		
		Button4 = ctk.CTkButton(self, text="Secure archive", text_color="white", fg_color="orange", border_width=2, border_color="white", width=170, height=32, font=my_font, command=self.create_secusbhelptextbox)
		Button4.place(relx=0.55, rely=0.2, anchor="center")
		
		Button5 = ctk.CTkButton(self, text="Digital ID\'s", text_color="white", fg_color="orange", border_width=2, border_color="white", width=170, height=32, font=my_font, command=self.create_digitalIDhelptextbox)
		Button5.place(relx=0.7, rely=0.2, anchor="center")
		
		Button6 = ctk.CTkButton(self, text="Bolt cards", text_color="white", fg_color="orange", border_width=2, border_color="white", width=170, height=32, font=my_font, command=self.create_boltcardhelptextbox)
		Button6.place(relx=0.85, rely=0.2, anchor="center")
	
	def create_GPGmeny(self):
		global GPG_button_color
		self.GnuPG_Home()
		my_font = ctk.CTkFont(family="Arial", size=16, weight="bold", slant="roman", underline=False, overstrike=False)
		
		CheckGPGButton = ctk.CTkButton(self, text="Check local keys", text_color="white", fg_color=GPG_button_color, border_width=2, border_color="white", width=170, height=32, font=my_font, command=self.get_GnuPGKeys)
		CheckGPGButton.place(relx=0.1, rely=0.2, anchor="center")
		
		AddkeyButton = ctk.CTkButton(self, text="Add/remove key", text_color="white", fg_color=GPG_button_color, border_width=2, border_color="white", width=170, height=32, font=my_font, command=self.newGPGFull_Key)
		AddkeyButton.place(relx=0.25, rely=0.2, anchor="center")
		
		AddsubkeyButton = ctk.CTkButton(self, text="Add subkeys", text_color="white", fg_color=GPG_button_color, border_width=2, border_color="white", width=170, height=32, font=my_font, command=self.newGPG_Subkey)
		AddsubkeyButton.place(relx=0.4, rely=0.2, anchor="center")
		
		BackupkeysButton = ctk.CTkButton(self, text="Backup keys", text_color="white", fg_color=GPG_button_color, border_width=2, border_color="white", width=170, height=32, font=my_font, command=self.backupGPG_Keys)
		BackupkeysButton.place(relx=0.55, rely=0.2, anchor="center")
		
		ImportkeyButton = ctk.CTkButton(self, text="Import/export", text_color="white", fg_color=GPG_button_color, border_width=2, border_color="white", width=170, height=32, font=my_font, command=self.import_or_export)
		ImportkeyButton.place(relx=0.7, rely=0.2, anchor="center")
		
		SignkeyButton = ctk.CTkButton(self, text="Sign/validate", text_color="white", fg_color=GPG_button_color, border_width=2, border_color="white", width=170, height=32, font=my_font, command=self.select_what_to_sign)
		SignkeyButton.place(relx=0.85, rely=0.2, anchor="center")
	
	def create_SecUSBmeny(self):
		global SecUSB_button_color
		global path_to_USB_secure
		
		self.create_secusbtextbox()
		my_font = ctk.CTkFont(family="Arial", size=16, weight="bold", slant="roman", underline=False, overstrike=False)
		
		Button1 = ctk.CTkButton(self, text="Secure archive", text_color="white", fg_color=SecUSB_button_color, border_width=2, border_color="white", width=170, height=32, font=my_font, command=self.check_SecUSB)
		Button1.place(relx=0.1, rely=0.2, anchor="center")
		
		Button2 = ctk.CTkButton(self, text="Encrypt/view a text", text_color="white", fg_color=SecUSB_button_color, border_width=2, border_color="white", width=170, height=32, font=my_font, command=self.encrypt_message)
		Button2.place(relx=0.25, rely=0.2, anchor="center")
		
		Button3 = ctk.CTkButton(self, text="Decrypt a textfile", text_color="white", fg_color=SecUSB_button_color, border_width=2, border_color="white", width=170, height=32, font=my_font, command=self.decrypt_message)
		Button3.place(relx=0.4, rely=0.2, anchor="center")
		
		Button4 = ctk.CTkButton(self, text="Restore from USB", text_color="white", fg_color=SecUSB_button_color, border_width=2, border_color="white", width=170, height=32, font=my_font, command=self.restoreFromencrypted_SecUSB)
		Button4.place(relx=0.55, rely=0.2, anchor="center")
		
		Button5 = ctk.CTkButton(self, text="Backup to USB/SD", text_color="white", fg_color=SecUSB_button_color, border_width=2, border_color="white", width=170, height=32, font=my_font, command=self.copy_SecUSB)
		Button5.place(relx=0.7, rely=0.2, anchor="center")
		
		Button6 = ctk.CTkButton(self, text="BTC wallets", text_color="white", fg_color=SecUSB_button_color, border_width=2, border_color="white", width=170, height=32, font=my_font, command=partial(self.create_Bitcointextbox, 'all'))
		Button6.place(relx=0.85, rely=0.2, anchor="center")
		
		if path_to_USB_secure == 'Secure USB folder is not available':
			Button8 = ctk.CTkButton(self, text="Log in", text_color="white", fg_color=SecUSB_button_color, border_width=2, border_color="white", width=170, height=32, font=my_font, command=self.decrypt_SecUSB)
			Button8.place(relx=0.5, rely=0.5, anchor="center")
			Label = ctk.CTkLabel(self, text="Or", text_color="white", font=("Helvetica", 18), fg_color="black")
			Label.place(relx=0.5, rely=0.55, anchor="center")
			Button7 = ctk.CTkButton(self, text="Create new user account", text_color="white", fg_color=SecUSB_button_color, border_width=2, border_color="white", width=170, height=32, font=my_font, command=self.new_secureUSB)
			Button7.place(relx=0.5, rely=0.6, anchor="center")
	
	def create_FIDOmeny(self):
		global FIDO_button_color
		global filepathdestinationfolder
		# The smaller frame
		my_Frame = ctk.CTkFrame(self, 
		width=1200, 
		height=650,
		border_width=2,
		border_color="brown"
		)
		my_Frame.place(relx=0.5, rely=0.6, anchor="center")
		
		left_Frame = ctk.CTkScrollableFrame(my_Frame, 
		width=278, 
		height=634,
		orientation="vertical",
		border_width=2,
		border_color="brown",
		fg_color="gray1"
		)
		left_Frame.place(relx=0, rely=0, anchor="nw")	
		
		pathtobackg = "/home/user1/venvpython/images/Yubikey5CBackground.JPG"
		if path_to_USB_secure == 'Secure USB folder is available':			
			completeName = str(filepathdestinationfolder) + "/secure/settings.csv"
			try:
				with open(completeName, 'r') as file:
					csvfile = csv.reader(file)
					for lines in csvfile:
						if lines:	
							users_theme = lines[1]
							users_colors = lines[2]
			except FileNotFoundError:
				messagebox.showinfo("Information", "No settings file found.")
			if users_theme == 'Winter':
				pathtobackg = "/home/user1/venvpython/images/winterbackgroundmid.jpg"
			if users_theme == 'Summer':
				pathtobackg = "/home/user1/venvpython/images/summerbackgroundmid.jpg"
			if users_theme == 'Light':
				pathtobackg = "/home/user1/venvpython/images/lightbackgroundmid.jpg"
			if users_theme == 'Dark':
				pathtobackg = "/home/user1/venvpython/images/darkbackgroundmid.jpg"
		
		backg = ctk.CTkImage(light_image=Image.open(pathtobackg), dark_image=Image.open(pathtobackg), size=(260, 630))
		Label_backg = ctk.CTkLabel(left_Frame, image=backg, text = "")
		Label_backg.place(x=2, y=2)
		
		right_Frame = ctk.CTkFrame(my_Frame, 
		width=900, 
		height=650,
		border_width=2,
		border_color="brown"
		)
		right_Frame.place(x=300, y=0, anchor="nw")
		pathtobackg = "/home/user1/venvpython/images/Yubikey5CBackground.JPG"
		
		backg = ctk.CTkImage(light_image=Image.open(pathtobackg), dark_image=Image.open(pathtobackg), size=(896, 646))
		Label_backg = ctk.CTkLabel(right_Frame, image=backg, text = "")
		Label_backg.place(x=2, y=2)
		my_font = ctk.CTkFont(family="Arial", size=16, weight="bold", slant="roman", underline=False, overstrike=False)
		
		my_font = ctk.CTkFont(family="Arial", size=20, slant="roman", underline=False, overstrike=False)
		
		if path_to_USB_secure == 'Secure USB folder is available':
			pathtoIDimage = str(filepathdestinationfolder) + "/venvpython/images/Yubikey5CBackground.JPG"

			IDimagebutton = ctk.CTkImage(light_image=Image.open(pathtoIDimage), dark_image=Image.open(pathtoIDimage), size=(230, 100))
			completeName = str(filepathdestinationfolder) + "/secure/FIDO/FIDOkeys.csv"
			my_font = ctk.CTkFont(family="Arial", size=16, weight="bold", slant="roman", underline=False, overstrike=False)
			counter = 0
			Buttonnew = ctk.CTkButton(right_Frame, text="New FIDO Key", text_color="white", fg_color="brown", border_width=2, border_color="white", width=150, height=20, font=my_font, command=self.newFIDO)
			Buttonnew.place(relx=0.9, rely=0.05, anchor="center")
			
			my_font = ctk.CTkFont(family="Arial", size=20, slant="roman", underline=True, overstrike=False)
			
			infoLabel = ctk.CTkLabel(right_Frame, text="Add new FIDO key:", text_color="white", font=my_font, fg_color="black")
			infoLabel.place(relx=0.1, rely=0.15, anchor="w")
			
			my_font = ctk.CTkFont(family="Arial", size=16, slant="roman", underline=False, overstrike=False)
			
			infoLabel = ctk.CTkLabel(right_Frame, text="1. Use a hardware key with FIDO2 support (ex. Yubikey 5 or similar).", text_color="white", font=my_font, fg_color="black")
			infoLabel.place(relx=0.1, rely=0.21, anchor="w")
			infoLabel2 = ctk.CTkLabel(right_Frame, text="   - Reset the key using an offline device (this will remove factory keys and generate new keys).", text_color="white", font=my_font, fg_color="black")
			infoLabel2.place(relx=0.1, rely=0.26, anchor="w")
			infoLabel3 = ctk.CTkLabel(right_Frame, text="2. - Register the FIDO-key at all services that the specific key work with.", text_color="white", font=my_font, fg_color="black")
			infoLabel3.place(relx=0.1, rely=0.32, anchor="w")
			infoLabel4 = ctk.CTkLabel(right_Frame, text="3. Remember to have at minimum two keys registered for each service, as one key could get lost/stolen or break.", text_color="white", font=my_font, fg_color="black")
			infoLabel4.place(relx=0.1, rely=0.41, anchor="w")
			infoLabel5 = ctk.CTkLabel(right_Frame, text="4. Add a new FIDO key entry on the offline device (this device) by clicking \"New FIDO key\".", text_color="white", font=my_font, fg_color="black")
			infoLabel5.place(relx=0.1, rely=0.46, anchor="w")
			infoLabel6 = ctk.CTkLabel(right_Frame, text="   - Give the FIDO key a name.", text_color="white", font=my_font, fg_color="black")
			infoLabel6.place(relx=0.1, rely=0.51, anchor="w")
			infoLabel7 = ctk.CTkLabel(right_Frame, text="   - Give the FIDO key a description.", text_color="white", font=my_font, fg_color="black")
			infoLabel7.place(relx=0.1, rely=0.56, anchor="w")
			infoLabel8 = ctk.CTkLabel(right_Frame, text="5. Enter the services that the key is registered at.", text_color="white", font=my_font, fg_color="black")
			infoLabel8.place(relx=0.1, rely=0.61, anchor="w")
			infoLabel9 = ctk.CTkLabel(right_Frame, text="   - This information is only to help in remembering what key is used for what.", text_color="white", font=my_font, fg_color="black")
			infoLabel9.place(relx=0.1, rely=0.66, anchor="w")
			infoLabel10 = ctk.CTkLabel(right_Frame, text="6. Keep the extra FIDO key(s) safe.", text_color="white", font=my_font, fg_color="black")
			infoLabel10.place(relx=0.1, rely=0.71, anchor="w")
			
			proLabel = ctk.CTkLabel(right_Frame, text="(Tip: FIDO keys are more secure as it is not as simple as stealing a password to gain access to an account.)", text_color="white", font=my_font, fg_color="black")
			proLabel.place(relx=0.1, rely=0.85, anchor="w")
			
			my_font = ctk.CTkFont(family="Arial", size=20, slant="roman", underline=True, overstrike=False)								
			cardLabel = ctk.CTkLabel(left_Frame, text="FIDO keys", text_color="white", font=my_font, fg_color="black").pack(padx=10, pady=8, side= TOP, anchor="center")
			my_font = ctk.CTkFont(family="Arial", size=16, slant="roman", underline=False, overstrike=False)
			Counting = 0
			try:
				with open(completeName, 'r') as file:
					csvfile = csv.reader(file)
					for lines in csvfile:
						if lines:
							if Counting == 0:	
								Button1 = ctk.CTkButton(left_Frame, text="", image = IDimagebutton, anchor='center', text_color="white", fg_color="brown", border_width=2, border_color="brown", width=220, height=100, font=my_font, command=partial(self.showFIDO, lines[0]))
								Button1.pack(padx=10, pady=18, side= TOP, anchor="w")
							else:
								Button1 = ctk.CTkButton(left_Frame, text="", image = IDimagebutton, anchor='center', text_color="white", fg_color="brown", border_width=2, border_color="brown", width=220, height=100, font=my_font, command=partial(self.showFIDO, lines[0]))
								Button1.pack(padx=10, pady=8, side= TOP, anchor="w")
							Counting += 1
			except FileNotFoundError:
				messagebox.showinfo("Information", "No FIDO Keys found.")
		else:
			notOKButton = ctk.CTkButton(right_Frame, text="You are not logged in.", text_color="white", fg_color="brown", border_width=2, border_color="white", width=170, height=32, font=my_font, command=self.decrypt_SecUSB)
			notOKButton.place(relx=0.5, rely=0.5, anchor="center")
	
	def showFIDO(self, FIDOname):
		global filepathdestinationfolder
		# The smaller frame
		my_Frame = ctk.CTkFrame(self, 
		width=1200, 
		height=650,
		border_width=1,
		border_color="brown"
		)
		my_Frame.place(relx=0.5, rely=0.6, anchor="center")
		
		left_Frame = ctk.CTkScrollableFrame(my_Frame, 
		width=278, 
		height=634,
		orientation="vertical",
		border_width=2,
		border_color="brown",
		fg_color="gray1"
		)
		left_Frame.place(relx=0, rely=0, anchor="nw")
		
		pathtobackg = "/home/user1/venvpython/images/darkbackgroundmid.jpg"
		backg = ctk.CTkImage(light_image=Image.open(pathtobackg), dark_image=Image.open(pathtobackg), size=(260, 630))
		Label_backg = ctk.CTkLabel(left_Frame, image=backg, text = "")
		Label_backg.place(x=2, y=2)
		
		right_Frame = ctk.CTkFrame(my_Frame, 
		width=900, 
		height=648,
		border_width=2,
		border_color="brown"
		)
		right_Frame.place(x=300, y=2, anchor="nw")
		
		pathtobackg = "/home/user1/venvpython/images/Yubikey5CBackground.JPG"
		if path_to_USB_secure == 'Secure USB folder is available':			
			completeName = str(filepathdestinationfolder) + "/secure/settings.csv"
			try:
				with open(completeName, 'r') as file:
					csvfile = csv.reader(file)
					for lines in csvfile:
						if lines:	
							users_theme = lines[1]
							users_colors = lines[2]
			except FileNotFoundError:
				messagebox.showinfo("Information", "No settings file found.")
			if users_theme == 'Winter':
				pathtobackg = "/home/user1/venvpython/images/winterbackgroundmid.jpg"
			if users_theme == 'Summer':
				pathtobackg = "/home/user1/venvpython/images/summerbackgroundmid.jpg"
			if users_theme == 'Light':
				pathtobackg = "/home/user1/venvpython/images/lightbackgroundmid.jpg"
			if users_theme == 'Dark':
				pathtobackg = "/home/user1/venvpython/images/darkbackgroundmid.jpg"
		
		backg = ctk.CTkImage(light_image=Image.open(pathtobackg), dark_image=Image.open(pathtobackg), size=(896, 646))
		Label_backg = ctk.CTkLabel(right_Frame, image=backg, text = "")
		Label_backg.place(x=0, y=0)
		my_font = ctk.CTkFont(family="Arial", size=16, weight="bold", slant="roman", underline=False, overstrike=False)
		
		if path_to_USB_secure == 'Secure USB folder is available':
			pathtoicon = str(filepathdestinationfolder) + "/venvpython/images/Yubikey5CBackground.JPG"

			iconimage = ctk.CTkImage(light_image=Image.open(pathtoicon), dark_image=Image.open(pathtoicon), size=(230, 100))
			
			completeName = str(filepathdestinationfolder) + "/secure/FIDO/FIDOkeys.csv"
			my_font = ctk.CTkFont(family="Arial", size=20, slant="roman", underline=True, overstrike=False)								
			cardLabel = ctk.CTkLabel(left_Frame, text="FIDO keys", text_color="white", font=my_font, fg_color="black").pack(padx=10, pady=8, side= TOP, anchor="center")
			my_font = ctk.CTkFont(family="Arial", size=16, slant="roman", underline=False, overstrike=False)
			Counting = 0
			try:
				with open(completeName, 'r') as file:
					csvfile = csv.reader(file)
					for lines in csvfile:
						if lines:
							if Counting == 0:	
								Button1 = ctk.CTkButton(left_Frame, text="", image = iconimage, anchor='center', text_color="white", fg_color="brown", border_width=2, border_color="brown", width=220, height=100, font=my_font, command=partial(self.showFIDO, lines[0]))
								Button1.pack(padx=10, pady=18, side= TOP, anchor="w")
							else:
								Button1 = ctk.CTkButton(left_Frame, text="", image = iconimage, anchor='center', text_color="white", fg_color="brown", border_width=2, border_color="brown", width=220, height=100, font=my_font, command=partial(self.showFIDO, lines[0]))
								Button1.pack(padx=10, pady=8, side= TOP, anchor="w")
							Counting += 1
			except FileNotFoundError:
				messagebox.showinfo("Information", "No FIDO Keys found.")
			Buttonnew = ctk.CTkButton(right_Frame, text="New FIDO key", text_color="white", fg_color="brown", border_width=2, border_color="white", width=150, height=20, font=my_font, command=self.newFIDO)
			Buttonnew.place(relx=0.9, rely=0.05, anchor="center")
			
			try:
				with open(completeName, 'r') as file:
					csvfile = csv.reader(file)
					for lines in csvfile:

						if lines[0] == FIDOname:								
							my_font = ctk.CTkFont(family="Arial", size=22, weight="bold", slant="roman", underline=True, overstrike=False)
							nameheadLabel = ctk.CTkLabel(right_Frame, text="Name of FIDO key:", text_color="white", font=my_font, fg_color="black")
							nameheadLabel.place(relx=0.05, rely=0.18, anchor="w")
							my_font = ctk.CTkFont(family="Arial", size=16, slant="roman", underline=False, overstrike=False)								
							nameLabel = ctk.CTkLabel(right_Frame, text=lines[0], text_color="white", font=my_font, fg_color="black")
							nameLabel.place(relx=0.05, rely=0.22, anchor="w")
							my_font = ctk.CTkFont(family="Arial", size=18, slant="roman", underline=True, overstrike=False)
							
							descrheadLabel = ctk.CTkLabel(right_Frame, text="Description:", text_color="white", font=my_font, fg_color="black")
							descrheadLabel.place(relx=0.05, rely=0.27, anchor="w")
							my_font = ctk.CTkFont(family="Arial", size=16, slant="roman", underline=False, overstrike=False)								
							descrLabel = ctk.CTkLabel(right_Frame, text=lines[1], text_color="white", font=my_font, fg_color="black")
							descrLabel.place(relx=0.05, rely=0.31, anchor="w")
							
							my_font = ctk.CTkFont(family="Arial", size=18, slant="roman", underline=True, overstrike=False)
							descrheadLabel = ctk.CTkLabel(right_Frame, text="Used for services:", text_color="white", font=my_font, fg_color="black")
							descrheadLabel.place(relx=0.05, rely=0.36, anchor="w")
							
							my_text = ctk.CTkTextbox(right_Frame, width=500, height=150, corner_radius=1, border_width=0, border_color="brown", border_spacing=2, fg_color="black", text_color="white", font=("Arial", 18), wrap="word", activate_scrollbars = True, scrollbar_button_color="grey75", scrollbar_button_hover_color="white")
							my_text.insert('end', lines[2])
							my_text.configure(state="disabled")
							my_text.place(relx=0.05, rely=0.4, anchor="nw")
														
							my_font = ctk.CTkFont(family="Arial", size=16, slant="roman", underline=False, overstrike=False)
							Buttonedit = ctk.CTkButton(right_Frame, text="Edit", text_color="white", fg_color="brown", border_width=2, border_color="white", width=150, height=32, font=my_font, command=partial(self.editFIDO, FIDOname))
							Buttonedit.place(relx=0.25, rely=0.85, anchor="center")
							delButton = ctk.CTkButton(right_Frame, text="Delete", text_color="white", fg_color="brown", border_width=2, border_color="white", width=170, height=32, font=my_font, command=partial(self.deleteFIDO, FIDOname))
							delButton.place(relx=0.5, rely=0.85, anchor="center")
							backButton = ctk.CTkButton(right_Frame, text="Back", text_color="white", fg_color="brown", border_width=2, border_color="white", width=170, height=32, font=my_font, command=self.create_FIDOmeny)
							backButton.place(relx=0.75, rely=0.85, anchor="center")
			except FileNotFoundError:
				messagebox.showinfo("Information", "No FIDO keys file found.")
		else:
			notOKButton = ctk.CTkButton(my_Frame, text="You are not logged in. Log in now?", text_color="white", fg_color="purple", border_width=2, border_color="white", width=170, height=32, font=my_font, command=self.decrypt_SecUSB)
			notOKButton.place(relx=0.5, rely=0.5, anchor="center")

	def editFIDO(self, FIDOname):
		global SecUSB_button_color
		global filepathdestinationfolder
		# The smaller frame
		my_Frame = ctk.CTkFrame(self, 
		width=1200, 
		height=650,
		border_width=4,
		border_color="blue"
		)
		my_Frame.place(relx=0.5, rely=0.6, anchor="center")
		theinput = ''
		my_text = ctk.CTkTextbox(my_Frame, width=500, height=150, corner_radius=1, border_width=0, border_color="brown", border_spacing=2, fg_color="black", text_color="white", font=("Arial", 18), wrap="word", activate_scrollbars = True, scrollbar_button_color="grey75", scrollbar_button_hover_color="white")
							
		def do_edit_FIDO():
			global filepathdestinationfolder
			Updated_name = nameEntry.get()
			Updated_description = descriptionEntry.get()
			theinput = self.textBox.get("1.0",'end-1c')
			
			Updated_FIDO_data = [
								Updated_name,
								Updated_description,
								theinput]
								
			completeName = str(filepathdestinationfolder) + "/secure/FIDO/FIDOkeys.csv"
			updatedcompleteName = str(filepathdestinationfolder) + "/secure/FIDO/updatedFIDOkeys.csv"
			with open(completeName, 'r') as source, open(updatedcompleteName, 'w') as result:
				csvreader = csv.reader(source)
				csvwriter = csv.writer(result)
				for row in csv.reader(source):
					try:
						if row[0] == FIDOname:
							csvwriter.writerow(Updated_FIDO_data)
						else:
							csvwriter.writerow(row)						
					except:
						continue
			shutil.copy(updatedcompleteName, completeName)
			os.remove(updatedcompleteName)	
			self.create_FIDOmeny()
		
		pathtobackg = "/home/user1/venvpython/images/Yubikey5CBackground.JPG"
		if path_to_USB_secure == 'Secure USB folder is available':			
			completeName = str(filepathdestinationfolder) + "/secure/settings.csv"
			try:
				with open(completeName, 'r') as file:
					csvfile = csv.reader(file)
					for lines in csvfile:
						if lines:	
							users_theme = lines[1]
							users_colors = lines[2]
			except FileNotFoundError:
				messagebox.showinfo("Information", "No settings file found.")
			if users_theme == 'Winter':
				pathtobackg = "/home/user1/venvpython/images/winterbackgroundmid.jpg"
			if users_theme == 'Summer':
				pathtobackg = "/home/user1/venvpython/images/summerbackgroundmid.jpg"
			if users_theme == 'Light':
				pathtobackg = "/home/user1/venvpython/images/lightbackgroundmid.jpg"
			if users_theme == 'Dark':
				pathtobackg = "/home/user1/venvpython/images/darkbackgroundmid.jpg"	
		
		backg = ctk.CTkImage(light_image=Image.open(pathtobackg), dark_image=Image.open(pathtobackg), size=(1200, 650))
		Label_backg = ctk.CTkLabel(my_Frame, image=backg, text = "")
		Label_backg.place(x=0, y=0)
		completeName = str(filepathdestinationfolder) + "/secure/FIDO/FIDOkeys.csv"
		# Read the content of the FIDO key in csv-file
		if path_to_USB_secure == 'Secure USB folder is available':
			try:
				with open(completeName, 'r') as file:
					csvfile = csv.reader(file)
					for lines in csvfile:
						if lines[0] == FIDOname:								
							my_font = ctk.CTkFont(family="Arial", size=22, weight="bold", slant="roman", underline=True, overstrike=False)
							nameheadLabel = ctk.CTkLabel(my_Frame, text="Edit FIDO key:", text_color="white", font=my_font, fg_color="black")
							nameheadLabel.place(relx=0.2, rely=0.1, anchor="w")
							
							my_font = ctk.CTkFont(family="Arial", size=18, slant="roman", underline=False, overstrike=False)
							nameheadLabel = ctk.CTkLabel(my_Frame, text="Name of FIDO key:", text_color="white", font=my_font, fg_color="black")
							nameheadLabel.place(relx=0.2, rely=0.18, anchor="w")
							
							my_font = ctk.CTkFont(family="Arial", size=16, slant="roman", underline=False, overstrike=False)								
							
							the_name_var = ctk.StringVar(value=lines[0])
		
							nameEntry = ctk.CTkEntry(my_Frame, placeholder_text=lines[0], textvariable=the_name_var, width=320, height=25, text_color="white", border_color="white", border_width=3, corner_radius=8, font=my_font)
							nameEntry.place(relx=0.2, rely=0.24, anchor="w")
							
							my_font = ctk.CTkFont(family="Arial", size=18, slant="roman", underline=False, overstrike=False)
							
							descrheadLabel = ctk.CTkLabel(my_Frame, text="Description:", text_color="white", font=my_font, fg_color="black")
							descrheadLabel.place(relx=0.2, rely=0.29, anchor="w")
							
							my_font = ctk.CTkFont(family="Arial", size=16, slant="roman", underline=False, overstrike=False)								
							
							the_description_var = ctk.StringVar(value=lines[1])
							
							descriptionEntry = ctk.CTkEntry(my_Frame, placeholder_text=lines[1], textvariable=the_description_var, width=320, height=25, text_color="white", border_color="white", border_width=3, corner_radius=8, font=my_font)
							descriptionEntry.place(relx=0.2, rely=0.33, anchor="w")
							
							my_font = ctk.CTkFont(family="Arial", size=18, slant="roman", underline=False, overstrike=False)
							descrheadLabel = ctk.CTkLabel(my_Frame, text="Used for services:", text_color="white", font=my_font, fg_color="black")
							descrheadLabel.place(relx=0.2, rely=0.38, anchor="w")
							
							self.textBox = Text(my_Frame, bg = "white", fg = "black", bd = 4, font=("Helvetica", 15), wrap = 'word', undo = True)
							self.textBox.insert("1.0", lines[2])
							self.textBox.place(relx=0.2, rely=0.42, height=220, width=600, anchor="nw")
							self.textBox.focus_set()
							self.textBox.focus_force()
							theinput = self.textBox.get("1.0",'end-1c')
							
							backButton = ctk.CTkButton(my_Frame, text="Save", text_color="white", fg_color="brown", border_width=2, border_color="white", width=170, height=32, font=my_font, command=do_edit_FIDO)
							backButton.place(relx=0.5, rely=0.85, anchor="center")
			except FileNotFoundError:
				messagebox.showinfo("Information", "No FIDO keys file found.")
		else:
			my_textbox.insert('end', 'You are not logged in. Cant edit.')
			
	def deleteFIDO(self, FIDOname):
		global filepathdestinationfolder
		completeName = str(filepathdestinationfolder) + "/secure/FIDO/FIDOkeys.csv"
		updatedcompleteName = str(filepathdestinationfolder) + "/secure/FIDO/updatedFIDOkeys.csv"
		with open(completeName, 'r') as source, open(updatedcompleteName, 'w') as result:
			csvreader = csv.reader(source)
			csvwriter = csv.writer(result)
			for row in csv.reader(source):
				try:
					if row[0] == FIDOname:
						answer = messagebox.askquestion('Important!', 'Are you sure you want to delete the FIDO key?')
						if answer == 'yes':
							print("Sure")
						else:
							csvwriter.writerow(row)
					else:
						csvwriter.writerow(row)						
				except:
					continue
		shutil.copy(updatedcompleteName, completeName)
		os.remove(updatedcompleteName)	
		self.create_FIDOmeny()
		
	def newFIDO(self):
		global filepathdestinationfolder
		# Create a new card. Details and pictures from USB-drive
		USER_INP = simpledialog.askstring(title="Name required!", prompt="Enter name for new FIDO key:")
		USER_INP2 = simpledialog.askstring(title="Description required!", prompt="Description for the new FIDO key:")
		
		new_FIDOkey = [USER_INP, USER_INP2, '<Empty>']
		completeName = str(filepathdestinationfolder) + "/secure/FIDO/FIDOkeys.csv"	
		try:
			f = open(completeName, 'a')
			writer = csv.writer(f)
			writer.writerow(new_FIDOkey)
			f.close()
		except FileNotFoundError:
			messagebox.showinfo("Information", "No FIDO keys file found.")
		self.create_FIDOmeny()
			
	def create_Boltcardmeny(self):
		global Boltcard_button_color
		global filepathdestinationfolder
		# The smaller frame
		my_Frame = ctk.CTkFrame(self, 
		width=1200, 
		height=650,
		border_width=2,
		border_color="brown"
		)
		my_Frame.place(relx=0.5, rely=0.6, anchor="center")
		
		left_Frame = ctk.CTkScrollableFrame(my_Frame, 
		width=278, 
		height=634,
		orientation="vertical",
		border_width=2,
		border_color="brown",
		fg_color="gray1"
		)
		left_Frame.place(relx=0, rely=0, anchor="nw")	
		
		pathtobackg = "/home/user1/venvpython/images/bluebackground.jpg"
		if path_to_USB_secure == 'Secure USB folder is available':			
			completeName = str(filepathdestinationfolder) + "/secure/settings.csv"
			try:
				with open(completeName, 'r') as file:
					csvfile = csv.reader(file)
					for lines in csvfile:
						if lines:	
							users_theme = lines[1]
							users_colors = lines[2]
			except FileNotFoundError:
				messagebox.showinfo("Information", "No settings file found.")
			if users_theme == 'Winter':
				pathtobackg = "/home/user1/venvpython/images/winterbackgroundmid.jpg"
			if users_theme == 'Summer':
				pathtobackg = "/home/user1/venvpython/images/summerbackgroundmid.jpg"
			if users_theme == 'Light':
				pathtobackg = "/home/user1/venvpython/images/lightbackgroundmid.jpg"
			if users_theme == 'Dark':
				pathtobackg = "/home/user1/venvpython/images/darkbackgroundmid.jpg"
		
		backg = ctk.CTkImage(light_image=Image.open(pathtobackg), dark_image=Image.open(pathtobackg), size=(260, 630))
		Label_backg = ctk.CTkLabel(left_Frame, image=backg, text = "")
		Label_backg.place(x=2, y=2)
		
		right_Frame = ctk.CTkFrame(my_Frame, 
		width=900, 
		height=650,
		border_width=2,
		border_color="brown"
		)
		right_Frame.place(x=300, y=0, anchor="nw")
		pathtobackg = "/home/user1/venvpython/images/boltcardbackground.JPG"
		
		backg = ctk.CTkImage(light_image=Image.open(pathtobackg), dark_image=Image.open(pathtobackg), size=(896, 646))
		Label_backg = ctk.CTkLabel(right_Frame, image=backg, text = "")
		Label_backg.place(x=2, y=2)
		my_font = ctk.CTkFont(family="Arial", size=16, weight="bold", slant="roman", underline=False, overstrike=False)
		
		my_font = ctk.CTkFont(family="Arial", size=20, slant="roman", underline=False, overstrike=False)
		
		if path_to_USB_secure == 'Secure USB folder is available':
			pathtoIDimage = str(filepathdestinationfolder) + "/venvpython/images/boltcardicon.JPG"

			IDimagebutton = ctk.CTkImage(light_image=Image.open(pathtoIDimage), dark_image=Image.open(pathtoIDimage), size=(230, 100))
			completeName = str(filepathdestinationfolder) + "/secure/boltcards/boltcards.csv"
			my_font = ctk.CTkFont(family="Arial", size=16, weight="bold", slant="roman", underline=False, overstrike=False)
			counter = 0
			Buttonnew = ctk.CTkButton(right_Frame, text="New card", text_color="white", fg_color="brown", border_width=2, border_color="white", width=150, height=20, font=my_font, command=self.newcard)
			Buttonnew.place(relx=0.9, rely=0.05, anchor="center")
			
			readButton = ctk.CTkButton(right_Frame, text="Read UID/URI", text_color="white", fg_color="brown", border_width=2, border_color="white", width=150, height=20, font=my_font, command=self.readUUID_with_NFC)
			readButton.place(relx=0.9, rely=0.11, anchor="center")
			
			my_font = ctk.CTkFont(family="Arial", size=20, slant="roman", underline=True, overstrike=False)
			
			infoLabel = ctk.CTkLabel(right_Frame, text="Create a new Bolt card:", text_color="white", font=my_font, fg_color="black")
			infoLabel.place(relx=0.1, rely=0.15, anchor="w")
			
			my_font = ctk.CTkFont(family="Arial", size=16, slant="roman", underline=False, overstrike=False)
			
			infoLabel = ctk.CTkLabel(right_Frame, text="1. Register a user account at a LNBits Hub (ex. lates.lightningok.win or similar).", text_color="white", font=my_font, fg_color="black")
			infoLabel.place(relx=0.1, rely=0.2, anchor="w")
			infoLabel2 = ctk.CTkLabel(right_Frame, text="   - Create a wallet, activate the extensions \"Bolts card\" and LNURLp.", text_color="white", font=my_font, fg_color="black")
			infoLabel2.place(relx=0.1, rely=0.24, anchor="w")
			infoLabel3 = ctk.CTkLabel(right_Frame, text="2. Use apps \"NFC tools\" and \"Bolt Card NFC Card Creator\" to make a card.", text_color="white", font=my_font, fg_color="black")
			infoLabel3.place(relx=0.1, rely=0.29, anchor="w")
			infoLabel4 = ctk.CTkLabel(right_Frame, text="3. With the data from your LNBits Hub- account make a text file with eight lines:", text_color="white", font=my_font, fg_color="black")
			infoLabel4.place(relx=0.1, rely=0.33, anchor="w")
			infoLabel4 = ctk.CTkLabel(right_Frame, text="   - LNURL link", text_color="white", font=my_font, fg_color="black")
			infoLabel4.place(relx=0.1, rely=0.37, anchor="w")
			infoLabel4 = ctk.CTkLabel(right_Frame, text="   - Reset code", text_color="white", font=my_font, fg_color="black")
			infoLabel4.place(relx=0.1, rely=0.41, anchor="w")
			infoLabel4 = ctk.CTkLabel(right_Frame, text="   - Program code", text_color="white", font=my_font, fg_color="black")
			infoLabel4.place(relx=0.1, rely=0.45, anchor="w")
			infoLabel4 = ctk.CTkLabel(right_Frame, text="   - Withdrawal limit", text_color="white", font=my_font, fg_color="black")
			infoLabel4.place(relx=0.1, rely=0.49, anchor="w")
			infoLabel4 = ctk.CTkLabel(right_Frame, text="   - Daily withdrawal limit", text_color="white", font=my_font, fg_color="black")
			infoLabel4.place(relx=0.1, rely=0.53, anchor="w")
			infoLabel4 = ctk.CTkLabel(right_Frame, text="   - Link to the Bolt Hub", text_color="white", font=my_font, fg_color="black")
			infoLabel4.place(relx=0.1, rely=0.57, anchor="w")
			infoLabel4 = ctk.CTkLabel(right_Frame, text="   - Bolt Hub user name", text_color="white", font=my_font, fg_color="black")
			infoLabel4.place(relx=0.1, rely=0.61, anchor="w")
			infoLabel4 = ctk.CTkLabel(right_Frame, text="   - Bolt Hub account password", text_color="white", font=my_font, fg_color="black")
			infoLabel4.place(relx=0.1, rely=0.65, anchor="w")
			infoLabel5 = ctk.CTkLabel(right_Frame, text="4. Using the text file, create a new Bolt card entry on the offline device by clicking \"New card\".", text_color="white", font=my_font, fg_color="black")
			infoLabel5.place(relx=0.1, rely=0.69, anchor="w")
			infoLabel5 = ctk.CTkLabel(right_Frame, text="Alt. You can receive an encrypted and signed file with above textlines and add it by clicking \"New card\".", text_color="white", font=my_font, fg_color="black")
			infoLabel5.place(relx=0.1, rely=0.74, anchor="w")
			
			proLabel = ctk.CTkLabel(right_Frame, text="(Pro tip1: If you get the file sent to you. Make sure it's encypted with your public key.)", text_color="white", font=my_font, fg_color="black")
			proLabel.place(relx=0.1, rely=0.8, anchor="w")
			proLabel2 = ctk.CTkLabel(right_Frame, text="(Pro tip2: Using https://ff.io or https://boltz.exchange/swap with swap from Liquid-BTC (l-BTC) will save on fees.)", text_color="white", font=my_font, fg_color="black")
			proLabel2.place(relx=0.1, rely=0.85, anchor="w")
			
			my_font = ctk.CTkFont(family="Arial", size=20, slant="roman", underline=True, overstrike=False)								
			cardLabel = ctk.CTkLabel(left_Frame, text="Bolt cards", text_color="white", font=my_font, fg_color="black").pack(padx=10, pady=8, side= TOP, anchor="center")
			my_font = ctk.CTkFont(family="Arial", size=16, slant="roman", underline=False, overstrike=False)
			Counting = 0
			try:
				with open(completeName, 'r') as file:
					csvfile = csv.reader(file)
					for lines in csvfile:
						if lines:
							if Counting == 0:	
								Button1 = ctk.CTkButton(left_Frame, text="", image = IDimagebutton, anchor='center', text_color="white", fg_color="brown", border_width=2, border_color="brown", width=220, height=100, font=my_font, command=partial(self.showcard, lines[0]))
								Button1.pack(padx=10, pady=18, side= TOP, anchor="w")
							else:
								Button1 = ctk.CTkButton(left_Frame, text="", image = IDimagebutton, anchor='center', text_color="white", fg_color="brown", border_width=2, border_color="brown", width=220, height=100, font=my_font, command=partial(self.showcard, lines[0]))
								Button1.pack(padx=10, pady=8, side= TOP, anchor="w")
							Counting += 1
			except FileNotFoundError:
				messagebox.showinfo("Information", "No Bolt cards file found.")
		else:
			notOKButton = ctk.CTkButton(right_Frame, text="You are not logged in.", text_color="white", fg_color="brown", border_width=2, border_color="white", width=170, height=32, font=my_font, command=self.decrypt_SecUSB)
			notOKButton.place(relx=0.5, rely=0.5, anchor="center")
	
	def showcard(self, cardname):
		global filepathdestinationfolder
		global pathtoloadaddress
		
		def save_load_QR():
			tk.messagebox.showinfo('Information', 'Insert the USB-device."')
			time.sleep(2)
			tk.messagebox.showinfo('Information', 'Select where to save the image with the load- address."')
			time.sleep(2)
			outputdir = filedialog.askdirectory(initialdir='/media/user1')
			pathtopic = outputdir + '/Boltcard_load_address.png'
			shutil.copy(pathtoloadaddress, pathtopic)
			
			if os.path.isfile(pathtopic):
				tk.messagebox.showinfo('Information', 'QR image has been saved."')
			
		# The smaller frame
		my_Frame = ctk.CTkFrame(self, 
		width=1200, 
		height=650,
		border_width=1,
		border_color="brown"
		)
		my_Frame.place(relx=0.5, rely=0.6, anchor="center")
		
		left_Frame = ctk.CTkScrollableFrame(my_Frame, 
		width=278, 
		height=634,
		orientation="vertical",
		border_width=2,
		border_color="brown",
		fg_color="gray1"
		)
		left_Frame.place(relx=0, rely=0, anchor="nw")
		
		pathtobackg = "/home/user1/venvpython/images/darkbackgroundmid.jpg"
		backg = ctk.CTkImage(light_image=Image.open(pathtobackg), dark_image=Image.open(pathtobackg), size=(260, 630))
		Label_backg = ctk.CTkLabel(left_Frame, image=backg, text = "")
		Label_backg.place(x=2, y=2)
		
		right_Frame = ctk.CTkFrame(my_Frame, 
		width=900, 
		height=650,
		border_width=2,
		border_color="brown"
		)
		right_Frame.place(x=300, y=0, anchor="nw")
		
		pathtobackg = "/home/user1/venvpython/images/boltcardbackground.JPG"
		if path_to_USB_secure == 'Secure USB folder is available':			
			completeName = str(filepathdestinationfolder) + "/secure/settings.csv"
			try:
				with open(completeName, 'r') as file:
					csvfile = csv.reader(file)
					for lines in csvfile:
						if lines:	
							users_theme = lines[1]
							users_colors = lines[2]
			except FileNotFoundError:
				messagebox.showinfo("Information", "No settings file found.")
			if users_theme == 'Winter':
				pathtobackg = "/home/user1/venvpython/images/winterbackgroundmid.jpg"
			if users_theme == 'Summer':
				pathtobackg = "/home/user1/venvpython/images/summerbackgroundmid.jpg"
			if users_theme == 'Light':
				pathtobackg = "/home/user1/venvpython/images/lightbackgroundmid.jpg"
			if users_theme == 'Dark':
				pathtobackg = "/home/user1/venvpython/images/darkbackgroundmid.jpg"
		
		backg = ctk.CTkImage(light_image=Image.open(pathtobackg), dark_image=Image.open(pathtobackg), size=(896, 646))
		Label_backg = ctk.CTkLabel(right_Frame, image=backg, text = "")
		Label_backg.place(x=0, y=0)
		my_font = ctk.CTkFont(family="Arial", size=16, weight="bold", slant="roman", underline=False, overstrike=False)
		
		if path_to_USB_secure == 'Secure USB folder is available':
			pathtoboltcardicon = str(filepathdestinationfolder) + "/venvpython/images/boltcardicon.JPG"

			boltcardiconimage = ctk.CTkImage(light_image=Image.open(pathtoboltcardicon), dark_image=Image.open(pathtoboltcardicon), size=(230, 100))
			
			completeName = str(filepathdestinationfolder) + "/secure/boltcards/boltcards.csv"
			my_font = ctk.CTkFont(family="Arial", size=16, weight="bold", slant="roman", underline=False, overstrike=False)
			try:
				with open(completeName, 'r') as file:
					csvfile = csv.reader(file)
					for lines in csvfile:
						if lines:	
							Button1 = ctk.CTkButton(left_Frame, text="", image = boltcardiconimage, anchor='center', text_color="white", fg_color="brown", border_width=2, border_color="white", width=220, height=100, font=my_font, command=partial(self.showcard, lines[0]))
							Button1.pack(padx=10, pady=8, side= TOP, anchor="w")
			except FileNotFoundError:
				messagebox.showinfo("Information", "No Bolt cards file found.")
			Buttonnew = ctk.CTkButton(right_Frame, text="New card", text_color="white", fg_color="brown", border_width=2, border_color="white", width=150, height=20, font=my_font, command=self.newcard)
			Buttonnew.place(relx=0.9, rely=0.05, anchor="center")
			try:
				with open(completeName, 'r') as file:
					csvfile = csv.reader(file)
					for lines in csvfile:
						try:
							if lines[0] == cardname:
								# Generate QR-codes for Public address and WIF-address and read them to display on screen
								load_address = qrcode.make(lines[3], version=1)
								reset_key = qrcode.make(lines[4], version=1)
								
								resize_load_address = load_address.resize((280, 280))
								resize_reset_key = reset_key.resize((300, 300))
								pathtoloadaddress = str(filepathdestinationfolder) + "/secure/boltcards/load.png"
								pathtoresetkey = str(filepathdestinationfolder) + "/secure/boltcards/reset.png"
								
								resize_load_address.save(pathtoloadaddress)
								resize_reset_key.save(pathtoresetkey)

								loadimg = ctk.CTkImage(light_image=Image.open(pathtoloadaddress), dark_image=Image.open(pathtoloadaddress), size=(280, 280))

								resetimg = ctk.CTkImage(light_image=Image.open(pathtoresetkey), dark_image=Image.open(pathtoresetkey), size=(300, 300))
								
								my_font = ctk.CTkFont(family="Arial", size=20, slant="roman", underline=True, overstrike=False)
			
								pubLabel = ctk.CTkLabel(right_Frame, text="Load (via Lightning network):", text_color="white", font=my_font, fg_color="black")
								pubLabel.place(relx=0.06, rely=0.12, anchor="w")
								Labelpublicimg = ctk.CTkLabel(right_Frame,  text = "", image = loadimg)
								Labelpublicimg.place(relx=0.2, rely=0.4, anchor="center")
								
								wifLabel = ctk.CTkLabel(right_Frame, text="Reset Boltcard:", text_color="white", font=my_font, fg_color="black")
								wifLabel.place(relx=0.74, rely=0.12, anchor="w")
								Labelwifimg = ctk.CTkLabel(right_Frame, text = "", image = resetimg)
								Labelwifimg.place(relx=0.8, rely=0.4, anchor="center")	
								
								my_font = ctk.CTkFont(family="Arial", size=22, weight="bold", slant="roman", underline=True, overstrike=False)
								nameheadLabel = ctk.CTkLabel(right_Frame, text="Name of Bolt card:", text_color="white", font=my_font, fg_color="black")
								nameheadLabel.place(relx=0.5, rely=0.18, anchor="center")
								my_font = ctk.CTkFont(family="Arial", size=16, slant="roman", underline=False, overstrike=False)								
								nameLabel = ctk.CTkLabel(right_Frame, text=lines[0], text_color="white", font=my_font, fg_color="black")
								nameLabel.place(relx=0.5, rely=0.22, anchor="center")
								my_font = ctk.CTkFont(family="Arial", size=18, slant="roman", underline=True, overstrike=False)
								
								descrheadLabel = ctk.CTkLabel(right_Frame, text="Description:", text_color="white", font=my_font, fg_color="black")
								descrheadLabel.place(relx=0.5, rely=0.27, anchor="center")
								my_font = ctk.CTkFont(family="Arial", size=16, slant="roman", underline=False, overstrike=False)								
								descrLabel = ctk.CTkLabel(right_Frame, text=lines[1], text_color="white", font=my_font, fg_color="black")
								descrLabel.place(relx=0.5, rely=0.31, anchor="center")
								
								my_font = ctk.CTkFont(family="Arial", size=18, slant="roman", underline=True, overstrike=False)
								descrheadLabel = ctk.CTkLabel(right_Frame, text="Max withrawal limit:", text_color="white", font=my_font, fg_color="black")
								descrheadLabel.place(relx=0.5, rely=0.36, anchor="center")
								my_font = ctk.CTkFont(family="Arial", size=16, slant="roman", underline=False, overstrike=False)								
								descrLabel = ctk.CTkLabel(right_Frame, text=lines[6], text_color="white", font=my_font, fg_color="black")
								descrLabel.place(relx=0.5, rely=0.4, anchor="center")
								
								my_font = ctk.CTkFont(family="Arial", size=18, slant="roman", underline=True, overstrike=False)
								descrheadLabel = ctk.CTkLabel(right_Frame, text="Max daily withrawal limit:", text_color="white", font=my_font, fg_color="black")
								descrheadLabel.place(relx=0.5, rely=0.45, anchor="center")
								my_font = ctk.CTkFont(family="Arial", size=16, slant="roman", underline=False, overstrike=False)								
								descrLabel = ctk.CTkLabel(right_Frame, text=lines[7], text_color="white", font=my_font, fg_color="black")
								descrLabel.place(relx=0.5, rely=0.49, anchor="center")
								
								my_font = ctk.CTkFont(family="Arial", size=18, slant="roman", underline=True, overstrike=False)
								dateheadLabel = ctk.CTkLabel(right_Frame, text="Created", text_color="white", font=my_font, fg_color="black")
								dateheadLabel.place(relx=0.5, rely=0.54, anchor="center")
								my_font = ctk.CTkFont(family="Arial", size=16, slant="roman", underline=False, overstrike=False)
								dateLabel = ctk.CTkLabel(right_Frame, text=lines[2], text_color="white", font=my_font, fg_color="black")
								dateLabel.place(relx=0.5, rely=0.58, anchor="center")
								
								saveQRButton = ctk.CTkButton(right_Frame, text="Save the Load QR-code to USB", text_color="white", fg_color="brown", border_width=2, border_color="white", font=my_font, command=save_load_QR)
								saveQRButton.place(relx=0.06, rely=0.66, anchor="w")
								my_font = ctk.CTkFont(family="Arial", size=16, weight="bold", slant="roman", underline=False, overstrike=False)
								programButton = ctk.CTkButton(right_Frame, text="Program (using Smartcard reader)", text_color="white", fg_color="brown", border_width=2, border_color="white", width=170, height=32, font=my_font, command=partial(self.programcard_with_NFC, cardname))
								programButton.place(relx=0.49, rely=0.72, anchor="center")
								programButton2 = ctk.CTkButton(right_Frame, text="Program (using a Smartphone)", text_color="white", fg_color="brown", border_width=2, border_color="white", width=170, height=32, font=my_font, command=partial(self.programcard, cardname))
								programButton2.place(relx=0.49, rely=0.78, anchor="center")
								delButton = ctk.CTkButton(right_Frame, text="Delete card", text_color="white", fg_color="brown", border_width=2, border_color="white", width=170, height=32, font=my_font, command=partial(self.deletecard, cardname))
								delButton.place(relx=0.49, rely=0.86, anchor="center")
								backButton = ctk.CTkButton(right_Frame, text="Back", text_color="white", fg_color="brown", border_width=2, border_color="white", width=170, height=32, font=my_font, command=self.create_Boltcardmeny)
								backButton.place(relx=0.49, rely=0.92, anchor="center")
						except:
							print("Cardname not found. Except.")
			except FileNotFoundError:
				messagebox.showinfo("Information", "No Bolt cards file found.")
		else:
			notOKButton = ctk.CTkButton(self, text="You are not logged in. Log in now?", text_color="white", fg_color="purple", border_width=2, border_color="white", width=170, height=32, font=my_font, command=self.decrypt_SecUSB)
			notOKButton.place(relx=0.5, rely=0.5, anchor="center")
	
	def readUUID_with_NFC(self):
		global filepathdestinationfolder
		
		# The smaller frame
		my_Frame = ctk.CTkFrame(self, 
		width=1200, 
		height=650,
		border_width=1,
		border_color="brown"
		)
		
		pathtobackg = "/home/user1/venvpython/images/bluebackground.jpg"
		if path_to_USB_secure == 'Secure USB folder is available':			
			completeName = str(filepathdestinationfolder) + "/secure/settings.csv"
			try:
				with open(completeName, 'r') as file:
					csvfile = csv.reader(file)
					for lines in csvfile:
						if lines:	
							users_theme = lines[1]
							users_colors = lines[2]
			except FileNotFoundError:
				messagebox.showinfo("Information", "No settings file found.")
			if users_theme == 'Winter':
				pathtobackg = "/home/user1/venvpython/images/winterbackgroundmid.jpg"
			if users_theme == 'Summer':
				pathtobackg = "/home/user1/venvpython/images/summerbackgroundmid.jpg"
			if users_theme == 'Light':
				pathtobackg = "/home/user1/venvpython/images/lightbackgroundmid.jpg"
			if users_theme == 'Dark':
				pathtobackg = "/home/user1/venvpython/images/darkbackgroundmid.jpg"
		backg = ctk.CTkImage(light_image=Image.open(pathtobackg), dark_image=Image.open(pathtobackg), size=(1200, 650))
		Label_backg = ctk.CTkLabel(my_Frame, image=backg, text = "")
		Label_backg.place(x=0, y=0)
		my_Frame.place(relx=0.5, rely=0.6, anchor="center")
		my_Frame.focus_set()
		my_Frame.focus_force()
		
		def do_readUUID_with_NFC():
			backg = ctk.CTkImage(light_image=Image.open(pathtobackg), dark_image=Image.open(pathtobackg), size=(1200, 650))
			Label_backg = ctk.CTkLabel(my_Frame, image=backg, text = "")
			Label_backg.place(x=0, y=0)

			bolt_uid = boltlib.read_uid()
			bolt_uri = boltlib.read_uri()
			my_font = ctk.CTkFont(family="Arial", size=20, slant="roman", underline=True, overstrike=False)
			waitLabel = ctk.CTkLabel(my_Frame, text='UUID:', text_color="white", font=my_font, fg_color="black")
			waitLabel.place(relx=0.5, rely=0.24, anchor="center")
			
			my_font = ctk.CTkFont(family="Arial", size=34, slant="roman", underline=False, overstrike=False)
			waitLabel = ctk.CTkLabel(my_Frame, text=bolt_uid, text_color="white", font=my_font, fg_color="black")
			waitLabel.place(relx=0.5, rely=0.36, anchor="center")
			
			my_font = ctk.CTkFont(family="Arial", size=20, slant="roman", underline=True, overstrike=False)
			waitLabel = ctk.CTkLabel(my_Frame, text='URI:', text_color="white", font=my_font, fg_color="black")
			waitLabel.place(relx=0.5, rely=0.56, anchor="center")
			my_font = ctk.CTkFont(family="Arial", size=16, slant="roman", underline=False, overstrike=False)
			waitLabel = ctk.CTkLabel(my_Frame, text=bolt_uri, text_color="white", font=my_font, fg_color="black")
			waitLabel.place(relx=0.5, rely=0.62, anchor="center")
			backButton = ctk.CTkButton(my_Frame, text="Back", text_color="white", fg_color="brown", border_width=2, border_color="white", width=170, height=32, font=my_font, command=self.create_Boltcardmeny)
			backButton.place(relx=0.5, rely=0.9, anchor="center")
			
		# Instructions to read URI from Bolt card with Smartcard reader
		my_font = ctk.CTkFont(family="Arial", size=20, slant="roman", underline=True, overstrike=False)

		Label = ctk.CTkLabel(my_Frame, text="Reading a Bolt card's URI and its UUID (Unique User Identification number) using a Smartcard reader *", text_color="white", font=my_font, fg_color="black")
		Label.place(relx=0.5, rely=0.2, anchor="center")
		my_font = ctk.CTkFont(family="Arial", size=18, slant="roman", underline=False, overstrike=False)
		Label2 = ctk.CTkLabel(my_Frame, text="(* Tested with HID Omnikey 5022 CL.)", text_color="white", font=my_font, fg_color="black")
		Label2.place(relx=0.5, rely=0.26, anchor="center")
		Label3 = ctk.CTkLabel(my_Frame, text='After pressing the \"Start\"- button, hold the Bolt card close to the Smartcard reader to read it.', text_color="white", font=my_font, fg_color="black")
		Label3.place(relx=0.5, rely=0.49, anchor="center")
		my_font = ctk.CTkFont(family="Arial", size=16, slant="roman", underline=False, overstrike=False)
		Label4 = ctk.CTkLabel(my_Frame, text='(Make sure that the Smartcard reader is connected.).', text_color="white", font=my_font, fg_color="black")
		Label4.place(relx=0.5, rely=0.54, anchor="center")
		my_font = ctk.CTkFont(family="Arial", size=20, slant="roman", underline=False, overstrike=False)
		backButton = ctk.CTkButton(my_Frame, text="Start", text_color="white", fg_color="brown", border_width=2, border_color="white", width=170, height=32, font=my_font, command=do_readUUID_with_NFC)
		backButton.place(relx=0.5, rely=0.6, anchor="center")
		my_font = ctk.CTkFont(family="Arial", size=16, slant="roman", underline=False, overstrike=False)
		backButton = ctk.CTkButton(my_Frame, text="Back", text_color="white", fg_color="brown", border_width=2, border_color="white", width=170, height=32, font=my_font, command=self.create_Boltcardmeny)
		backButton.place(relx=0.5, rely=0.9, anchor="center")
		
	def programcard_with_NFC(self, cardname):
		global filepathdestinationfolder
		global theURI
		
		theURI = ''
		print(cardname)
		completeName = str(filepathdestinationfolder) + "/secure/boltcards/boltcards.csv"
		updatedcompleteName = str(filepathdestinationfolder) + "/secure/boltcards/updatedboltcards.csv"
		
		# The smaller frame
		my_Frame = ctk.CTkFrame(self, 
		width=1200, 
		height=650,
		border_width=1,
		border_color="brown"
		)
		
		pathtobackg = "/home/user1/venvpython/images/bluebackground.jpg"
		if path_to_USB_secure == 'Secure USB folder is available':			
			completeName = str(filepathdestinationfolder) + "/secure/settings.csv"
			try:
				with open(completeName, 'r') as file:
					csvfile = csv.reader(file)
					for lines in csvfile:
						if lines:	
							users_theme = lines[1]
							users_colors = lines[2]
			except FileNotFoundError:
				messagebox.showinfo("Information", "No settings file found.")
			if users_theme == 'Winter':
				pathtobackg = "/home/user1/venvpython/images/winterbackgroundmid.jpg"
			if users_theme == 'Summer':
				pathtobackg = "/home/user1/venvpython/images/summerbackgroundmid.jpg"
			if users_theme == 'Light':
				pathtobackg = "/home/user1/venvpython/images/lightbackgroundmid.jpg"
			if users_theme == 'Dark':
				pathtobackg = "/home/user1/venvpython/images/darkbackgroundmid.jpg"
		backg = ctk.CTkImage(light_image=Image.open(pathtobackg), dark_image=Image.open(pathtobackg), size=(1200, 650))
		Label_backg = ctk.CTkLabel(my_Frame, image=backg, text = "")
		Label_backg.place(x=0, y=0)
		my_Frame.place(relx=0.5, rely=0.6, anchor="center")
		my_Frame.focus_set()
		my_Frame.focus_force()
		
		def do_programcard_with_NFC():
			global theURI
			backg = ctk.CTkImage(light_image=Image.open(pathtobackg), dark_image=Image.open(pathtobackg), size=(1200, 650))
			Label_backg = ctk.CTkLabel(my_Frame, image=backg, text = "")
			Label_backg.place(x=0, y=0)
			waitLabel = ctk.CTkLabel(my_Frame, text='Waiting for smartcard.....', text_color="white", font=my_font, fg_color="black")
			waitLabel.place(relx=0.5, rely=0.37, anchor="center")
			my_Frame.focus_set()
			my_Frame.focus_force()
			write_uri = boltlib.write_uri(theURI)

			self.create_Boltcardmeny()
		
		completeName = str(filepathdestinationfolder) + "/secure/boltcards/boltcards.csv"
		try:
			with open(completeName, 'r') as file:
				csvfile = csv.reader(file)
				for lines in csvfile:
					if lines[0] == cardname:
						theURI = lines[3]					
		except FileNotFoundError:
			messagebox.showinfo("Information", "No Bolt cards file found.")
			
		# Instructions Bolt card programming with Smartcard reader
		my_font = ctk.CTkFont(family="Arial", size=20, slant="roman", underline=True, overstrike=False)

		Label = ctk.CTkLabel(my_Frame, text="Programming a Bolt card with only a receive address (LNURL) using a Smartcard reader *", text_color="white", font=my_font, fg_color="black")
		Label.place(relx=0.5, rely=0.2, anchor="center")
		my_font = ctk.CTkFont(family="Arial", size=18, slant="roman", underline=False, overstrike=False)
		Label2 = ctk.CTkLabel(my_Frame, text="(* Tested with HID Omnikey 5022 CL. For now, full programming is not available unless using smartphone with app.)", text_color="white", font=my_font, fg_color="black")
		Label2.place(relx=0.5, rely=0.26, anchor="center")
		Label3 = ctk.CTkLabel(my_Frame, text='After pressing the \"Start\"- button, hold the card close to the Smartcard reader to program it.', text_color="white", font=my_font, fg_color="black")
		Label3.place(relx=0.5, rely=0.49, anchor="center")
		my_font = ctk.CTkFont(family="Arial", size=16, slant="roman", underline=False, overstrike=False)
		Label4 = ctk.CTkLabel(my_Frame, text='(Make sure that the Smartcard reader is connected.).', text_color="white", font=my_font, fg_color="black")
		Label4.place(relx=0.5, rely=0.54, anchor="center")
		my_font = ctk.CTkFont(family="Arial", size=18, slant="roman", underline=False, overstrike=False)
		backButton = ctk.CTkButton(my_Frame, text="Start", text_color="white", fg_color="brown", border_width=2, border_color="white", width=170, height=32, font=my_font, command=do_programcard_with_NFC)
		backButton.place(relx=0.5, rely=0.6, anchor="center")
		backButton = ctk.CTkButton(my_Frame, text="Back", text_color="white", fg_color="brown", border_width=2, border_color="white", width=170, height=32, font=my_font, command=self.create_Boltcardmeny)
		backButton.place(relx=0.5, rely=0.9, anchor="center")
		
	def programcard(self, cardname):
		global filepathdestinationfolder
		completeName = str(filepathdestinationfolder) + "/secure/boltcards/boltcards.csv"
		updatedcompleteName = str(filepathdestinationfolder) + "/secure/boltcards/updatedboltcards.csv"
		# The smaller frame
		my_Frame = ctk.CTkFrame(self, 
		width=1200, 
		height=650,
		border_width=1,
		border_color="brown"
		)
		
		pathtobackg = "/home/user1/venvpython/images/bluebackground.jpg"
		if path_to_USB_secure == 'Secure USB folder is available':			
			completeName = str(filepathdestinationfolder) + "/secure/settings.csv"
			try:
				with open(completeName, 'r') as file:
					csvfile = csv.reader(file)
					for lines in csvfile:
						if lines:	
							users_theme = lines[1]
							users_colors = lines[2]
			except FileNotFoundError:
				messagebox.showinfo("Information", "No settings file found.")
			if users_theme == 'Winter':
				pathtobackg = "/home/user1/venvpython/images/winterbackgroundmid.jpg"
			if users_theme == 'Summer':
				pathtobackg = "/home/user1/venvpython/images/summerbackgroundmid.jpg"
			if users_theme == 'Light':
				pathtobackg = "/home/user1/venvpython/images/lightbackgroundmid.jpg"
			if users_theme == 'Dark':
				pathtobackg = "/home/user1/venvpython/images/darkbackgroundmid.jpg"
		
		backg = ctk.CTkImage(light_image=Image.open(pathtobackg), dark_image=Image.open(pathtobackg), size=(1200, 650))
		Label_backg = ctk.CTkLabel(my_Frame, image=backg, text = "")
		Label_backg.place(x=0, y=0)
		my_Frame.place(relx=0.5, rely=0.6, anchor="center")
		my_Frame.focus_set()
		my_Frame.focus_force()
		
		completeName = str(filepathdestinationfolder) + "/secure/boltcards/boltcards.csv"
		try:
			with open(completeName, 'r') as file:
				csvfile = csv.reader(file)
				for lines in csvfile:
					try:
						if lines[0] == cardname:
							# Generate QR-code for programming the bolt card, display on screen
							program_QRpic = qrcode.make(lines[5], version=1)
							
							resized_program_QRpic = program_QRpic.resize((320, 320))

							pathtoprogramaddress = str(filepathdestinationfolder) + "/secure/boltcards/program.png"
							
							resized_program_QRpic.save(pathtoprogramaddress)

							programimg = ctk.CTkImage(light_image=Image.open(pathtoprogramaddress), dark_image=Image.open(pathtoprogramaddress), size=(320, 320))

							my_font = ctk.CTkFont(family="Arial", size=20, slant="roman", underline=True, overstrike=False)
		
							pubLabel = ctk.CTkLabel(my_Frame, text="Program (via smartphone app *)", text_color="white", font=my_font, fg_color="black")
							pubLabel.place(relx=0.5, rely=0.05, anchor="center")
							my_font = ctk.CTkFont(family="Arial", size=18, slant="roman", underline=False, overstrike=False)
							pubLabel = ctk.CTkLabel(my_Frame, text="(* Bolt Card NFC Card Creator- app from App/Play-store)", text_color="white", font=my_font, fg_color="black")
							pubLabel.place(relx=0.5, rely=0.1, anchor="center")
							Labelpublicimg = ctk.CTkLabel(my_Frame,  text = "", image = programimg)
							Labelpublicimg.place(relx=0.5, rely=0.4, anchor="center")
							desLabel = ctk.CTkLabel(my_Frame, text='Bolt Hub link: ' + lines[8], text_color="white", font=my_font, fg_color="black")
							desLabel.place(relx=0.5, rely=0.72, anchor="center")
							desLabel = ctk.CTkLabel(my_Frame, text='Bolt Hub User name: ' + lines[9], text_color="white", font=my_font, fg_color="black")
							desLabel.place(relx=0.5, rely=0.77, anchor="center")
							desLabel = ctk.CTkLabel(my_Frame, text='Bolt Hub user password: ' + lines[10], text_color="white", font=my_font, fg_color="black")
							desLabel.place(relx=0.5, rely=0.82, anchor="center")
					except:
							print("Cardname not found. Except.")
							
		except FileNotFoundError:
			messagebox.showinfo("Information", "No Bolt cards file found.")
		
		backButton = ctk.CTkButton(my_Frame, text="Back", text_color="white", fg_color="brown", border_width=2, border_color="white", width=170, height=32, font=my_font, command=self.create_Boltcardmeny)
		backButton.place(relx=0.5, rely=0.9, anchor="center")
		
	def deletecard(self, cardname):
		global filepathdestinationfolder
		completeName = str(filepathdestinationfolder) + "/secure/boltcards/boltcards.csv"
		updatedcompleteName = str(filepathdestinationfolder) + "/secure/boltcards/updatedboltcards.csv"
		with open(completeName, 'r') as source, open(updatedcompleteName, 'w') as result:
			csvreader = csv.reader(source)
			csvwriter = csv.writer(result)
			for row in csv.reader(source):
				try:
					if row[0] == cardname:
						answer = messagebox.askquestion('Important!', 'Are you sure you want to delete the Bolt card?')
						if answer == 'yes':
							print("Not sure")
						else:
							csvwriter.writerow(row)
					else:
						csvwriter.writerow(row)						
				except:
					continue
		shutil.copy(updatedcompleteName, completeName)
		os.remove(updatedcompleteName)	
		self.create_Boltcardmeny()
		
	def newcard(self):
		global filepathdestinationfolder
		# Create a new card. Details and pictures from USB-drive
		USER_INP = simpledialog.askstring(title="Name required!", prompt="Name for the new Bolt card:")
		USER_INP2 = simpledialog.askstring(title="Description required!", prompt="Description for the new Bolt card:")
			
		answer = messagebox.askquestion('Information!', 'Is the Bolt card data in a signed and encrypted file?')
			
		if answer == 'yes':
			try:
				messagebox.showinfo("Bolt card data required", "Connect the USB-device. Select the encrypted file with the Bolt card data.")
				time.sleep(3)
				filepathdatafile = filedialog.askopenfilename(initialdir='/media/user1')
				completeTempName = filepathdestinationfolder + '/secure/boltcards/boltcardtemp.txt'
				gpg = gnupg.GPG(gnupghome='/home/user1/.gnupg/')
				# Decrypt the file and output it to a temporary file
				data_ = gpg.decrypt_file(filepathdatafile, output=completeTempName)
				# Check if data was OK
				if data_.ok:
					if data_.trust_level is not None and data_.trust_level >= data_.TRUST_FULLY:
						# If the trust for the signature key is OK then read the temporary file and split into lines
						try:
							lines = open(completeTempName).read().splitlines()
						except IOError:
							messagebox.showinfo("Information", "There was a problem reading the file!")
						
						if len(lines) == 8:
							completeName = filepathdestinationfolder + "/secure/boltcards/boltcards.csv"
							thedate = str(date.today())

							new_boltcard = [USER_INP, USER_INP2, thedate, lines[0], lines[1], lines[2], lines[3], lines[4], lines[5], lines[6], lines[7]]
							
							f = open(completeName, 'a')
							writer = csv.writer(f)
							writer.writerow(new_boltcard)
							f.close()
							messagebox.showinfo("Information", "Success! Signature (Key ID: " + data_.key_id + ") is good. New Bolt card added.")
							self.create_Boltcardmeny()
						else:
							messagebox.showinfo("Information", "There was a problem reading the decrypted content! \nMake sure that it contains exactly eight lines of data.")
					else:
						messagebox.showinfo("Alert!", "Signature could not be verified!")
						self.create_Boltcardmeny()
				else:
					messagebox.showinfo('Information', data_.status)
					self.create_Boltcardmeny()
			except IOError:
				messagebox.showinfo("Information", "There was a problem reading the file!")
		else:
			messagebox.showinfo("Bolt card data required", "Connect the USB-device. Select the file with the Bolt card data.")
			time.sleep(3)
			filepathdatafile = filedialog.askopenfilename(initialdir='/media/user1')
			
			try:
				lines = open(filepathdatafile).read().splitlines()
			except IOError:
				messagebox.showinfo("Information", "There was a problem reading the file!")
			if len(lines) == 8:
				completeName = filepathdestinationfolder + "/secure/boltcards/boltcards.csv"
				thedate = str(date.today())

				new_boltcard = [USER_INP, USER_INP2, thedate, lines[0],lines[1],lines[2],lines[3], lines[4], lines[5],lines[6],lines[7]]
				
				f = open(completeName, 'a')
				writer = csv.writer(f)
				writer.writerow(new_boltcard)
				f.close()
			else:
				messagebox.showinfo("Information", "There was a problem reading the file! \nMake sure there is exactly eight lines with the required data in the file?")
			
		self.create_Boltcardmeny()
						
	def create_DigitalIDmeny(self):
		global DigitalID_button_color
		global filepathdestinationfolder
		# The smaller frame
		my_Frame = ctk.CTkFrame(self, 
		width=1200, 
		height=650,
		border_width=0,
		border_color="blue"
		)
		my_Frame.place(relx=0.5, rely=0.6, anchor="center")
		my_Frame.focus_set()
		my_Frame.focus_force()
		
		left_Frame = ctk.CTkScrollableFrame(my_Frame, 
		width=278, 
		height=634,
		orientation="vertical",
		border_width=2,
		border_color="brown",
		fg_color="gray1"
		)
		left_Frame.place(relx=0, rely=0, anchor="nw")		
		
		pathtobackg = "/home/user1/venvpython/images/bluebackground.jpg"
		if path_to_USB_secure == 'Secure USB folder is available':			
			completeName = str(filepathdestinationfolder) + "/secure/settings.csv"
			try:
				with open(completeName, 'r') as file:
					csvfile = csv.reader(file)
					for lines in csvfile:
						if lines:	
							users_theme = lines[1]
							users_colors = lines[2]
			except FileNotFoundError:
				messagebox.showinfo("Information", "No settings file found.")
			if users_theme == 'Winter':
				pathtobackg = "/home/user1/venvpython/images/winterbackgroundmid.jpg"
			if users_theme == 'Summer':
				pathtobackg = "/home/user1/venvpython/images/summerbackgroundmid.jpg"
			if users_theme == 'Light':
				pathtobackg = "/home/user1/venvpython/images/lightbackgroundmid.jpg"
			if users_theme == 'Dark':
				pathtobackg = "/home/user1/venvpython/images/darkbackgroundmid.jpg"
		
		backg = ctk.CTkImage(light_image=Image.open(pathtobackg), dark_image=Image.open(pathtobackg), size=(260, 630))
		Label_backg = ctk.CTkLabel(left_Frame, image=backg, text = "")
		Label_backg.place(x=2, y=2)
		
		right_Frame = ctk.CTkFrame(my_Frame, 
		width=900, 
		height=650,
		border_width=2,
		border_color="brown"
		)
		right_Frame.place(x=300, y=0, anchor="nw")
		pathtobackg = "/home/user1/venvpython/images/bluebackground.jpg"
		if path_to_USB_secure == 'Secure USB folder is available':			
			completeName = str(filepathdestinationfolder) + "/secure/settings.csv"
			try:
				with open(completeName, 'r') as file:
					csvfile = csv.reader(file)
					for lines in csvfile:
						if lines:	
							users_theme = lines[1]
							users_colors = lines[2]
			except FileNotFoundError:
				messagebox.showinfo("Information", "No settings file found.")
			if users_theme == 'Winter':
				pathtobackg = "/home/user1/venvpython/images/winterbackgroundmid.jpg"
			if users_theme == 'Summer':
				pathtobackg = "/home/user1/venvpython/images/summerbackgroundmid.jpg"
			if users_theme == 'Light':
				pathtobackg = "/home/user1/venvpython/images/lightbackgroundmid.jpg"
			if users_theme == 'Dark':
				pathtobackg = "/home/user1/venvpython/images/darkbackgroundmid.jpg"
		
		backg = ctk.CTkImage(light_image=Image.open(pathtobackg), dark_image=Image.open(pathtobackg), size=(896, 646))
		Label_backg = ctk.CTkLabel(right_Frame, image=backg, text = "")
		Label_backg.place(x=2, y=2)
		
		my_font = ctk.CTkFont(family="Arial", size=20, slant="roman", underline=False, overstrike=False)
		
		pathtoIDimage = str(filepathdestinationfolder) + "/venvpython/images/DemoID.JPG"
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
